Jahjahhhh/projet5/table-2/kicad_libraries/My_Libraries/Header_cassable_4Short_pins__simpleAG2 v1.step

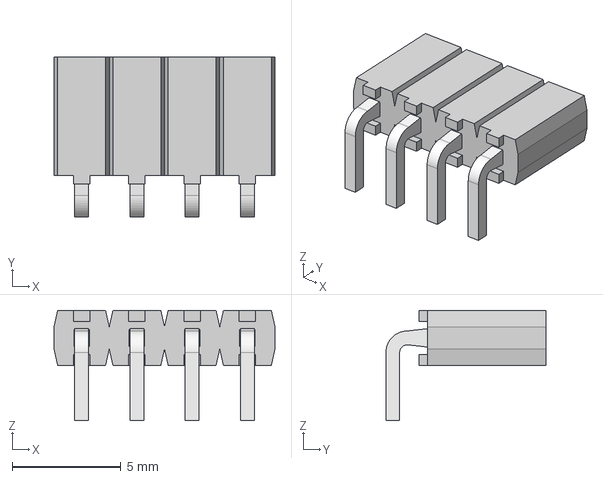
[picture p16: CAD file, 2024-10-07]
table-2/kicad_libraries/My_Libraries/Header_cassable_4Short_pins__simpleAG2 v1.step
10.2 x 7.37 x 5.08 mm
_SSA-132-W-T-RA_t
_SSA-132-W-T-RA_p
