Jahjahhhh/projet5/table-2/kicad_libraries/My_Libraries/SOT_223_5.STEP

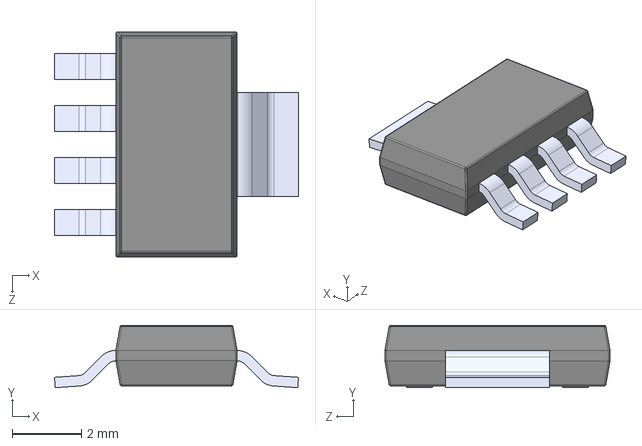
[picture p17: CAD file, 2024-10-07]
table-2/kicad_libraries/My_Libraries/SOT_223_5.STEP
7.04 x 1.80 x 6.50 mm
