Jahjahhhh/projet5/table-2/kicad_libraries/My_Libraries/cree xlamp_xp_e.stl

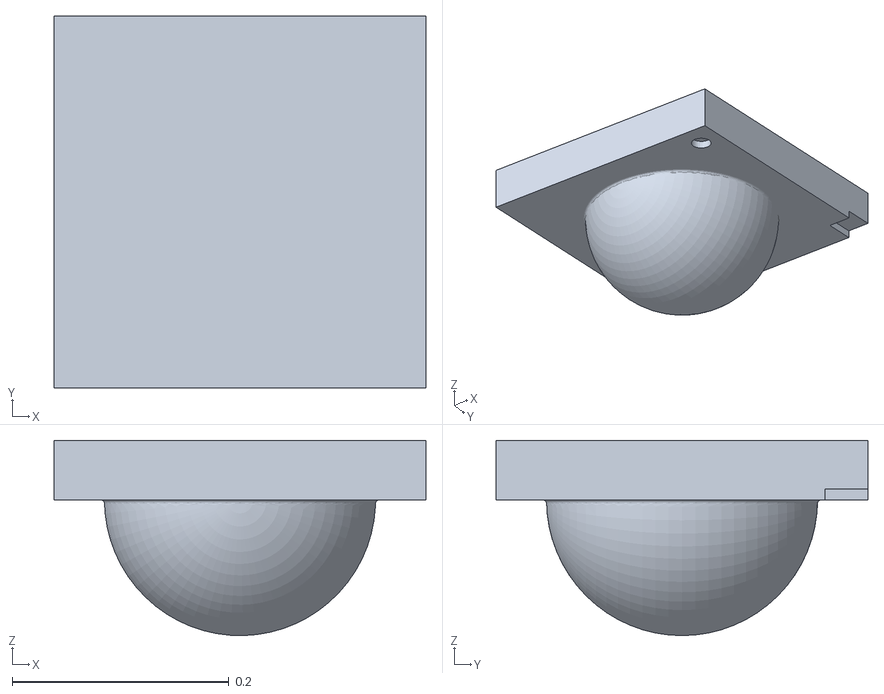
[picture p18: CAD file, 2024-10-07]
table-2/kicad_libraries/My_Libraries/cree xlamp_xp_e.stl
0.343 x 0.343 x 0.18
