Jahjahhhh/projet5/table-2/kicad_libraries/My_Libraries/b3f-6020AG.step

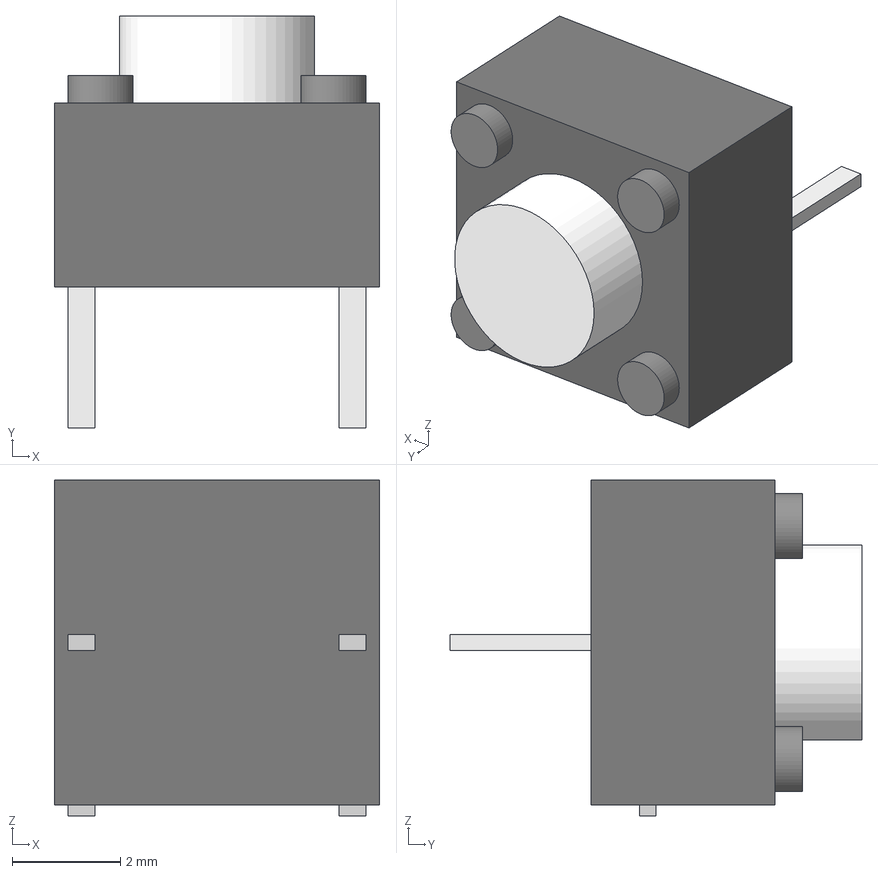
[picture p19: CAD file, 2024-10-07]
table-2/kicad_libraries/My_Libraries/b3f-6020AG.step
6.00 x 7.60 x 6.20 mm
