Jahjahhhh/projet5/table-2/kicad_libraries/My_Libraries/RELAY_ALQ3_PANVA.step

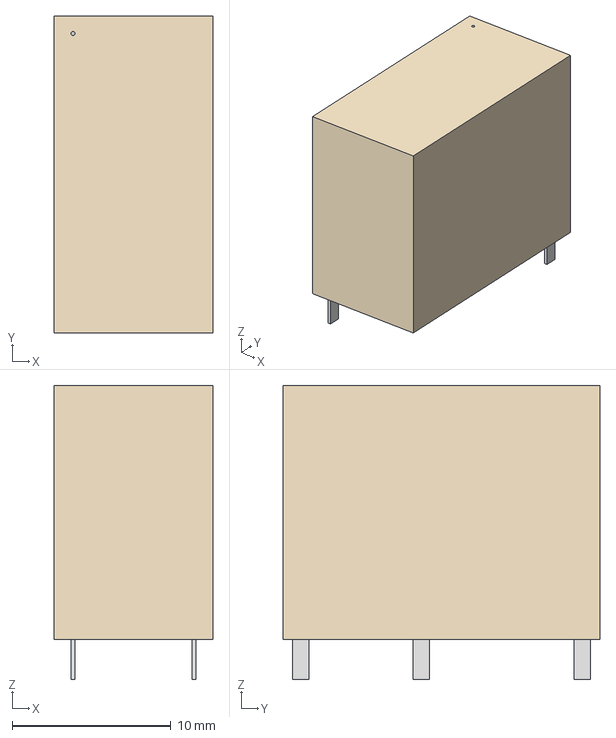
[picture p20: CAD file, 2024-10-07]
table-2/kicad_libraries/My_Libraries/RELAY_ALQ3_PANVA.step
10.0 x 20.0 x 18.5 mm
