Jahjahhhh/projet5/table-2/kicad_libraries/My_Libraries/Nichicon_5x11_LeadAG.step

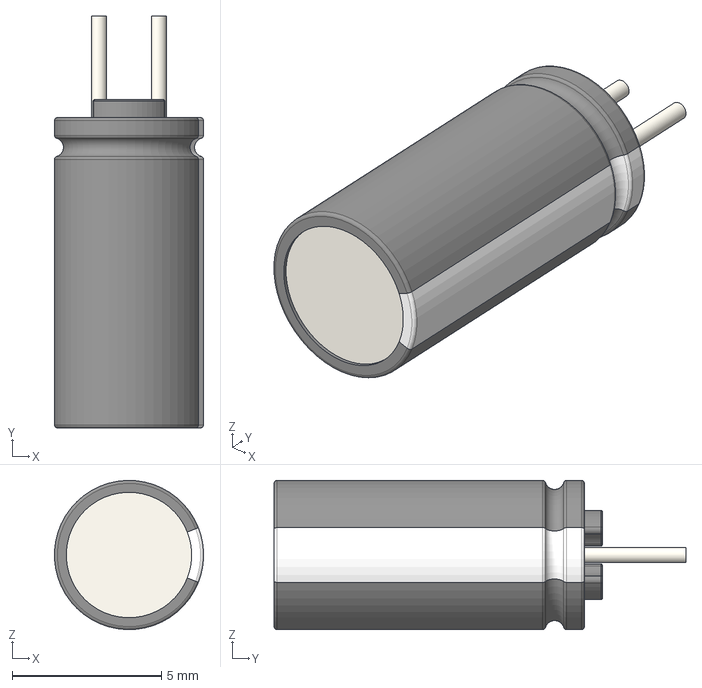
[picture p21: CAD file, 2024-10-07]
table-2/kicad_libraries/My_Libraries/Nichicon_5x11_LeadAG.step
4.99 x 13.8 x 5.00 mm
