Jahjahhhh/projet5/table-2/kicad_libraries/My_Libraries/XTAL_HC49US_ABLS_ABR.step

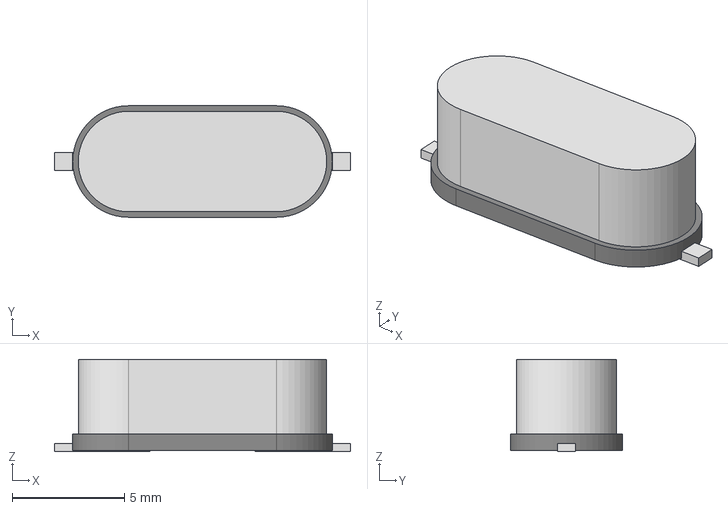
[picture p22: CAD file, 2024-10-07]
table-2/kicad_libraries/My_Libraries/XTAL_HC49US_ABLS_ABR.step
13.2 x 4.98 x 4.12 mm
