Jahjahhhh/projet5/table-2/kicad_libraries/My_Libraries/MEM2075-00-140-01-A.stp

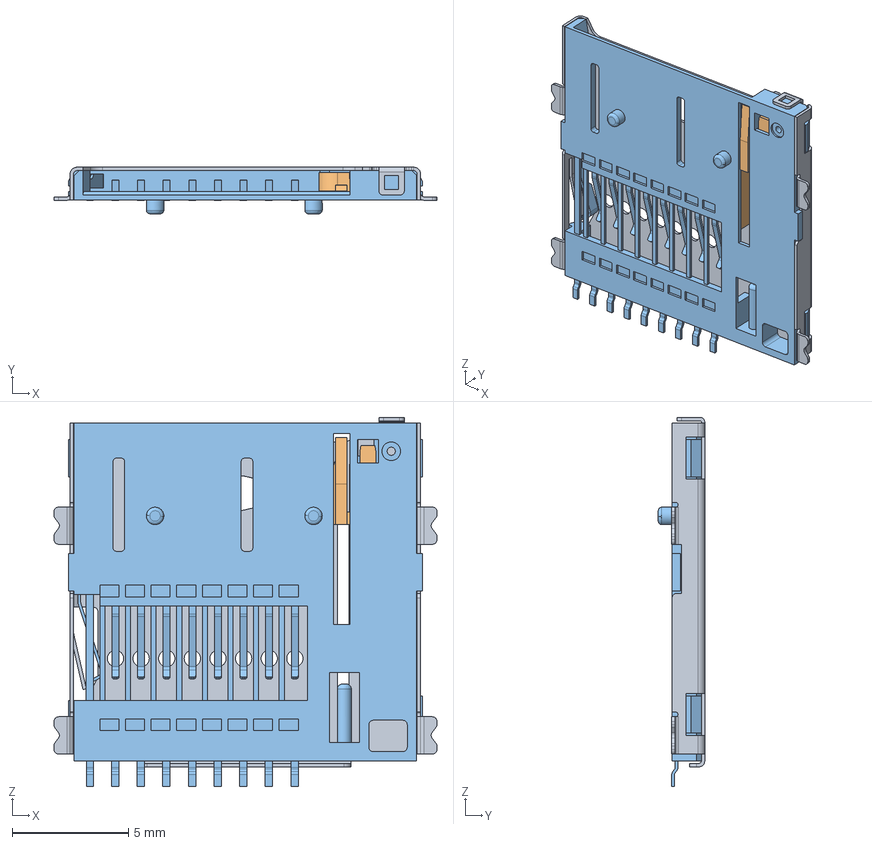
[picture p23: CAD file, 2024-10-07]
table-2/kicad_libraries/My_Libraries/MEM2075-00-140-01-A.stp
16.4 x 2.00 x 15.9 mm
Ëõ·Å±ÈÀý1
Í¹Ì¨-ÀÉì1
Á¬½ÓÖØ×é1
