Jahjahhhh/projet5/table-2/kicad_libraries/My_Libraries/c-1776252-2-a-3d.stp

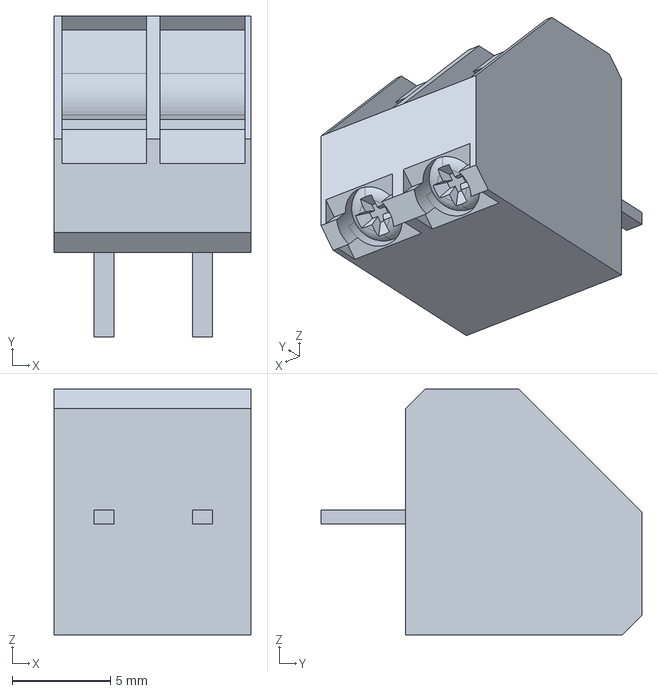
[picture p24: CAD file, 2024-10-07]
table-2/kicad_libraries/My_Libraries/c-1776252-2-a-3d.stp
10.0 x 16.3 x 12.5 mm
