Jahjahhhh/projet5/table-2/kicad_libraries/My_Libraries/3214J.stp

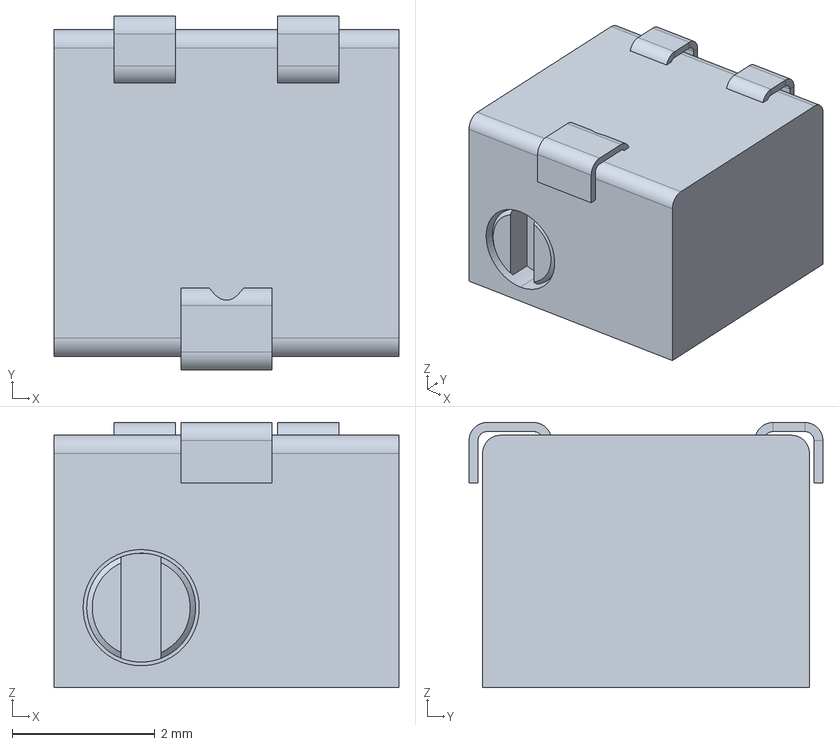
[picture p25: CAD file, 2024-10-07]
table-2/kicad_libraries/My_Libraries/3214J.stp
4.83 x 4.95 x 3.71 mm
