Jahjahhhh/projet5/table-2/kicad_libraries/My_Libraries/ESQ-118-14-G-D.stp

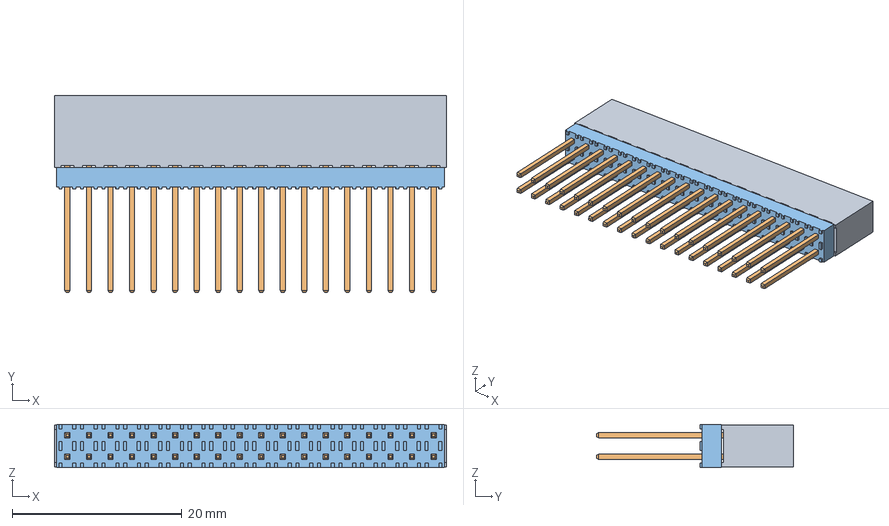
[picture p26: CAD file, 2024-10-07]
table-2/kicad_libraries/My_Libraries/ESQ-118-14-G-D.stp
46.2 x 23.2 x 5.08 mm
_ESQ-118-14-G-D_socket
_ESQ-118-14-G-D_pins
_ESQ-118-14-G-D-LL_bpins
