Jahjahhhh/projet5/table-2/kicad_libraries/My_Libraries/User Library-XBeeProS1-1.STEP

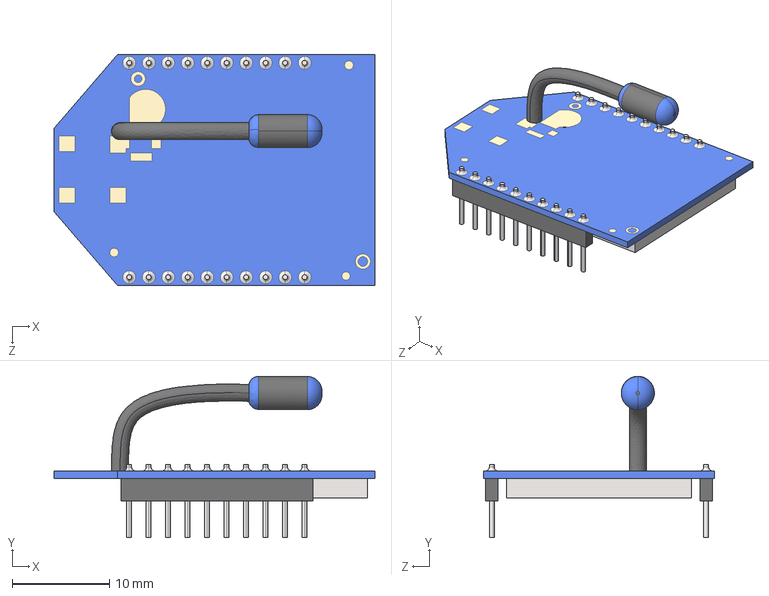
[picture p27: CAD file, 2024-10-07]
table-2/kicad_libraries/My_Libraries/User Library-XBeeProS1-1.STEP
32.9 x 16.6 x 23.7 mm
