Jahjahhhh/projet5/table-2/kicad_libraries/My_Libraries/USB3145-30-0-A.stp

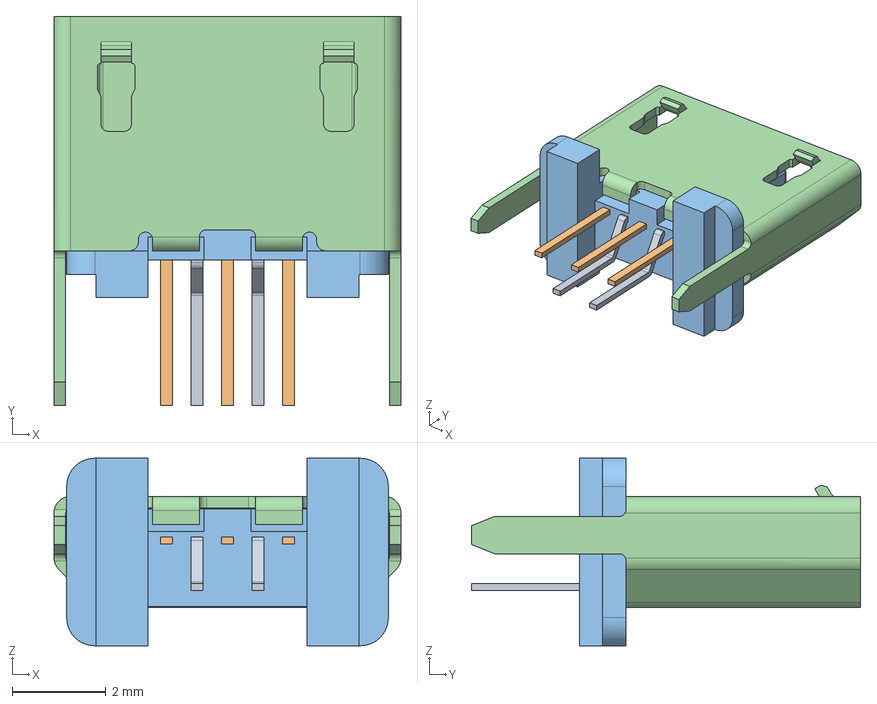
[picture p28: CAD file, 2024-10-07]
table-2/kicad_libraries/My_Libraries/USB3145-30-0-A.stp
7.40 x 8.30 x 4.00 mm
Imported1 x 5
移动面1
倒角1
