Jahjahhhh/projet5/table-2/kicad_libraries/My_Libraries/1-1825027-1_Bouton_Bleu v1.step

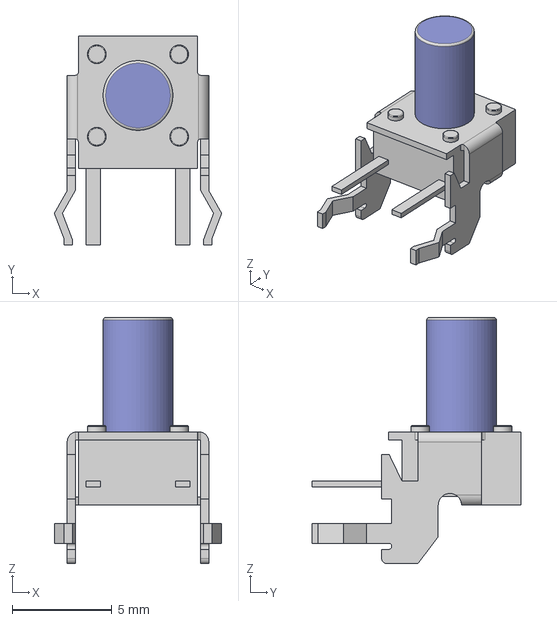
[picture p29: CAD file, 2024-10-07]
table-2/kicad_libraries/My_Libraries/1-1825027-1_Bouton_Bleu v1.step
8.41 x 10.5 x 12.4 mm
