Jahjahhhh/projet5/table-2/kicad_libraries/My_Libraries/B2B-ZR.STEP

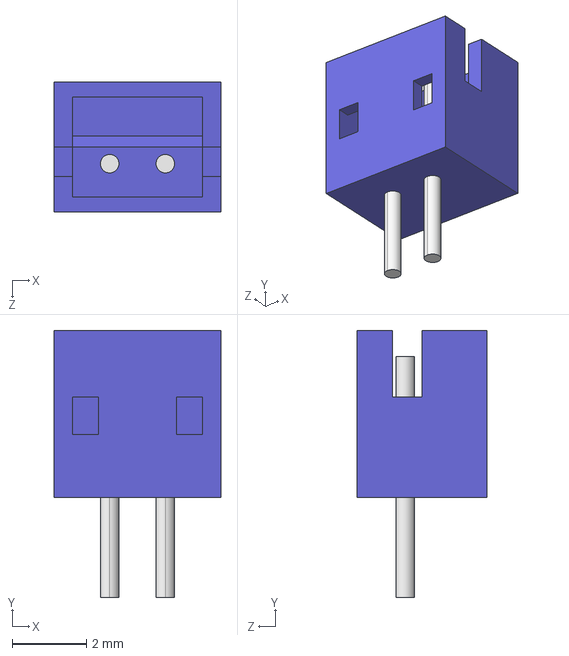
[picture p30: CAD file, 2024-10-07]
table-2/kicad_libraries/My_Libraries/B2B-ZR.STEP
4.50 x 7.20 x 3.50 mm
