Jahjahhhh/projet5/table-2/kicad_libraries/My_Libraries/c-1776252-3-a-3d.stp

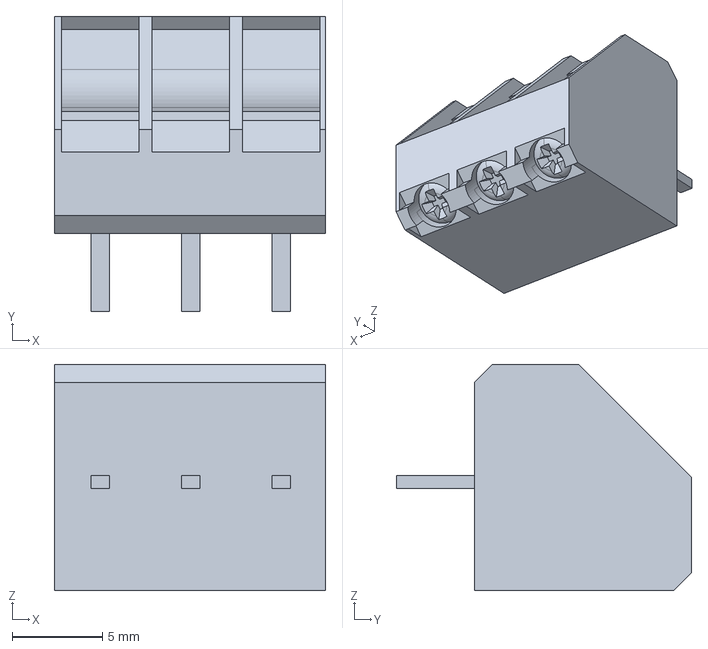
[picture p31: CAD file, 2024-10-07]
table-2/kicad_libraries/My_Libraries/c-1776252-3-a-3d.stp
15.0 x 16.3 x 12.5 mm
