Jahjahhhh/projet5/table-2/kicad_libraries/My_Libraries/panasonic_ALQ1.STEP

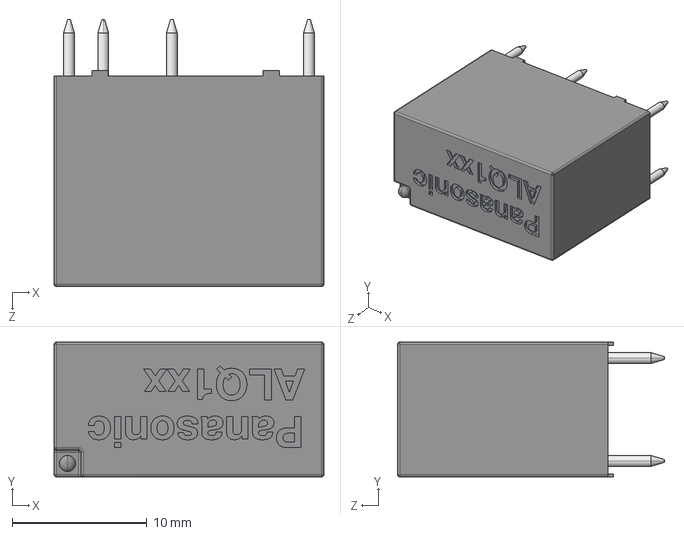
[picture p32: CAD file, 2024-10-07]
table-2/kicad_libraries/My_Libraries/panasonic_ALQ1.STEP
20.0 x 10.0 x 19.8 mm
