Jahjahhhh/projet5/table-2/kicad_libraries/My_Libraries/pxc_1984989_04_PTSA-1-5-4-3-5-F_3D.stp

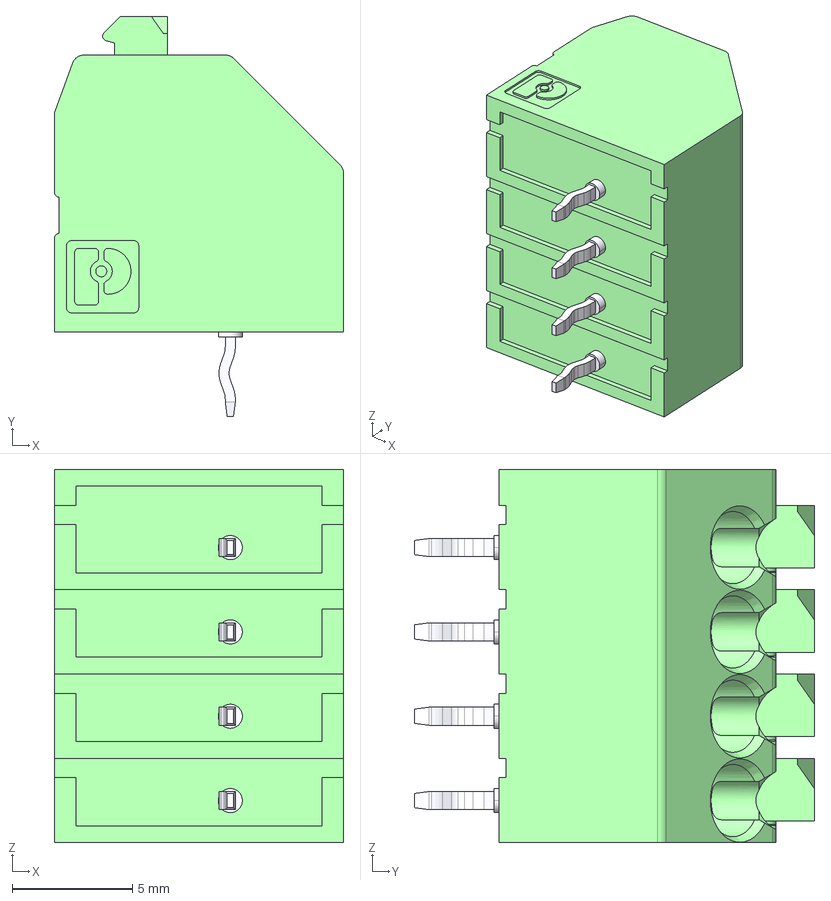
[picture p33: CAD file, 2024-10-07]
table-2/kicad_libraries/My_Libraries/pxc_1984989_04_PTSA-1-5-4-3-5-F_3D.stp
12.0 x 16.6 x 15.5 mm
