Jahjahhhh/projet5/table-2/kicad_libraries/My_Libraries/Barrel_Wurth_5_5X2_1mm.stp

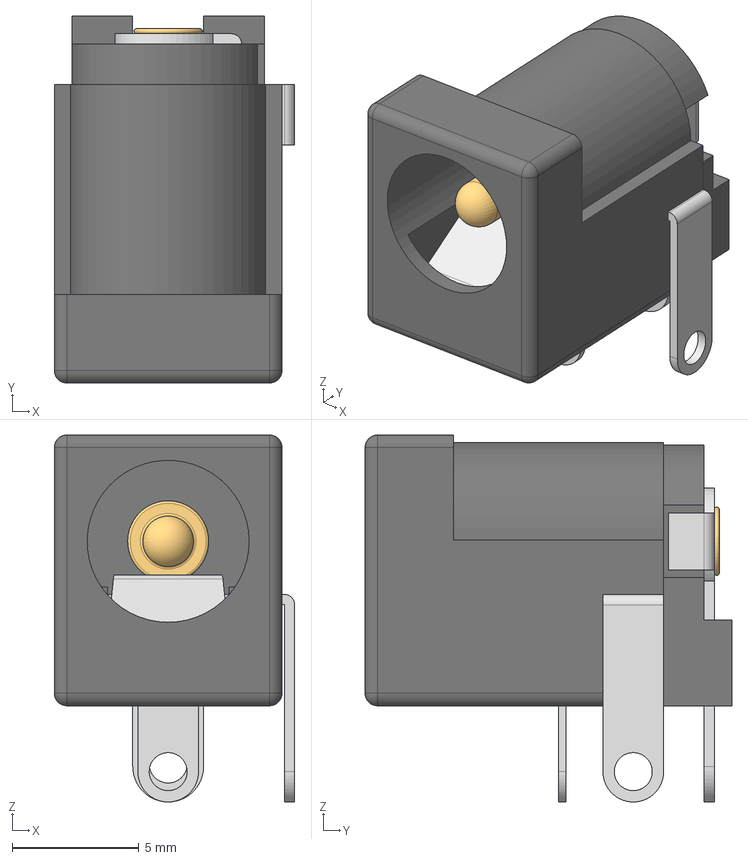
[picture p34: CAD file, 2024-10-07]
table-2/kicad_libraries/My_Libraries/Barrel_Wurth_5_5X2_1mm.stp
9.50 x 14.5 x 14.5 mm
6941xx301002
694106301002_PinContact
6941xx301002_Back
6941xx301002_PinContact2
6941xx301002_PinLame
6941xx301002_PinBis
