Jahjahhhh/projet5/table-2/kicad_libraries/My_Libraries/Stabilizer_close.STEP

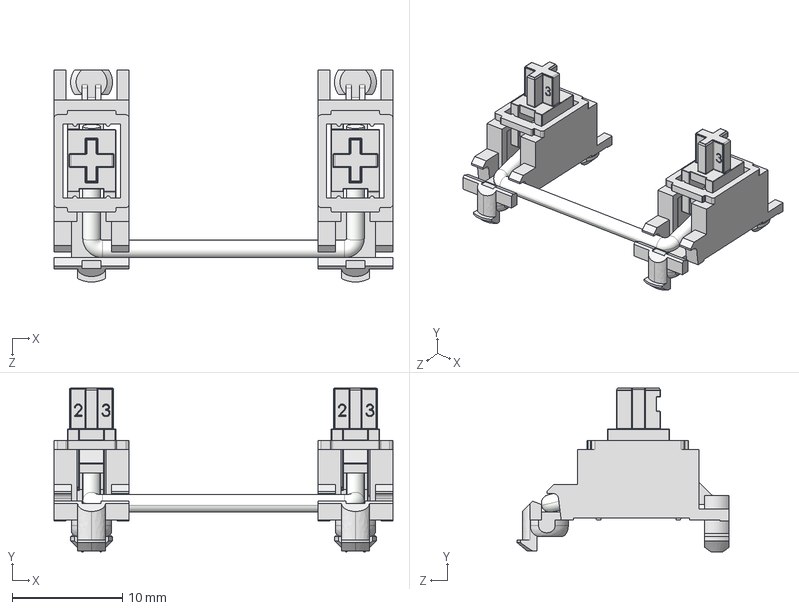
[picture p35: CAD file, 2024-10-07]
table-2/kicad_libraries/My_Libraries/Stabilizer_close.STEP
30.7 x 14.9 x 19.2 mm
mx Stabilizer base 16828 x 2
mx Stabilizer key 16828 x 2
metal stick 16828
