Jahjahhhh/projet5/table-2/kicad_libraries/My_Libraries/PianoSpring_v33.step

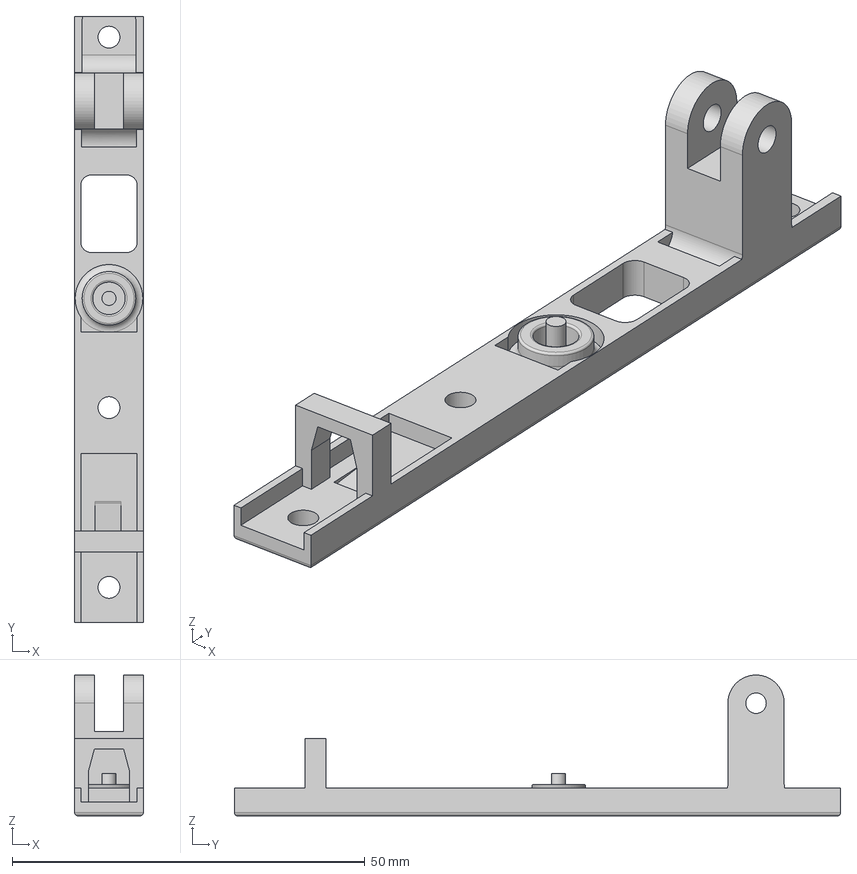
[picture p36: CAD file, 2024-10-07]
table-2/kicad_libraries/My_Libraries/PianoSpring_v33.step
9.75 x 86.0 x 20.0 mm
