Jahjahhhh/projet5/table-2/kicad_libraries/My_Libraries/Adafruit_BNO055__Avec_Header4et6.step

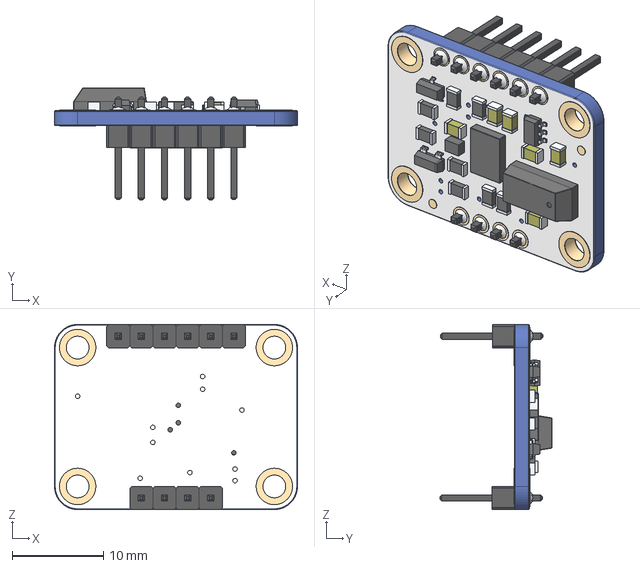
[picture p37: CAD file, 2024-10-07]
table-2/kicad_libraries/My_Libraries/Adafruit_BNO055__Avec_Header4et6.step
26.7 x 12.3 x 20.3 mm
Pin (1) x 4
Pin (1)_1 x 6
