Jahjahhhh/projet5/table-2/kicad_libraries/My_Libraries/1-1318300-2.stp

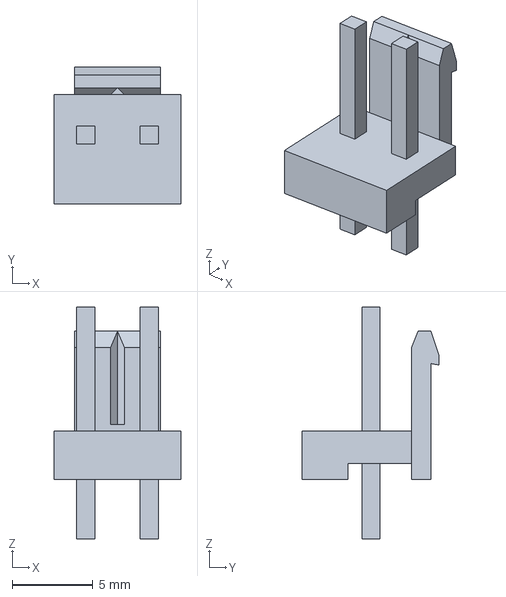
[picture p38: CAD file, 2024-10-07]
table-2/kicad_libraries/My_Libraries/1-1318300-2.stp
7.86 x 8.50 x 14.4 mm
