Jahjahhhh/projet5/table-2/kicad_libraries/My_Libraries/ENCODEUR.STEP

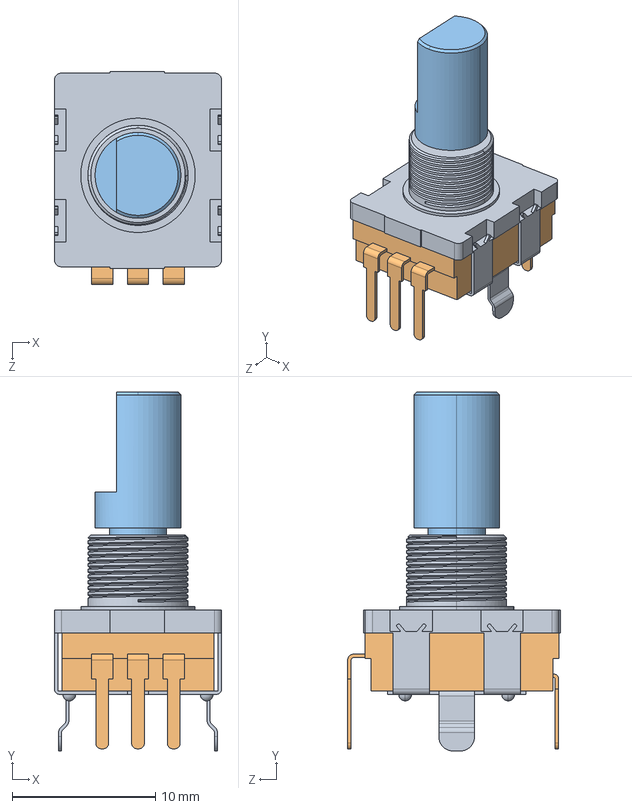
[picture p39: CAD file, 2024-10-07]
table-2/kicad_libraries/My_Libraries/ENCODEUR.STEP
11.7 x 25.1 x 14.9 mm
