Jahjahhhh/projet5/table-2/kicad_libraries/My_Libraries/SM04B_56544.STEP

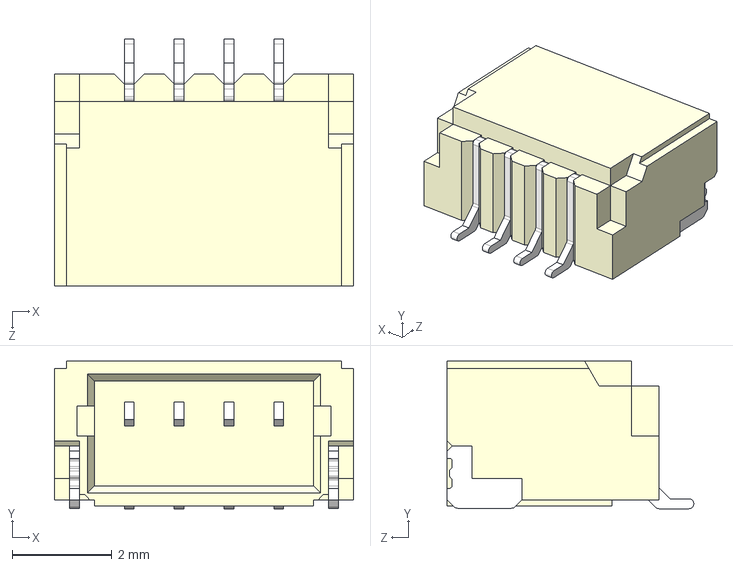
[picture p40: CAD file, 2024-10-07]
table-2/kicad_libraries/My_Libraries/SM04B_56544.STEP
6.00 x 2.96 x 4.95 mm
