Jahjahhhh/projet5/table-2/kicad_libraries/My_Libraries/PS30-10PB1BR10K.stp

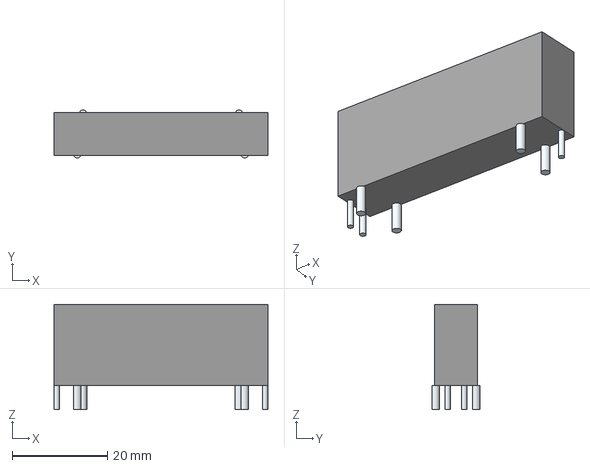
[picture p41: CAD file, 2024-10-07]
table-2/kicad_libraries/My_Libraries/PS30-10PB1BR10K.stp
45.0 x 10.1 x 22.1 mm
Leads x 7
