Jahjahhhh/projet5/table-2/kicad_libraries/My_Libraries/TS6-SMT_H-6.0.step

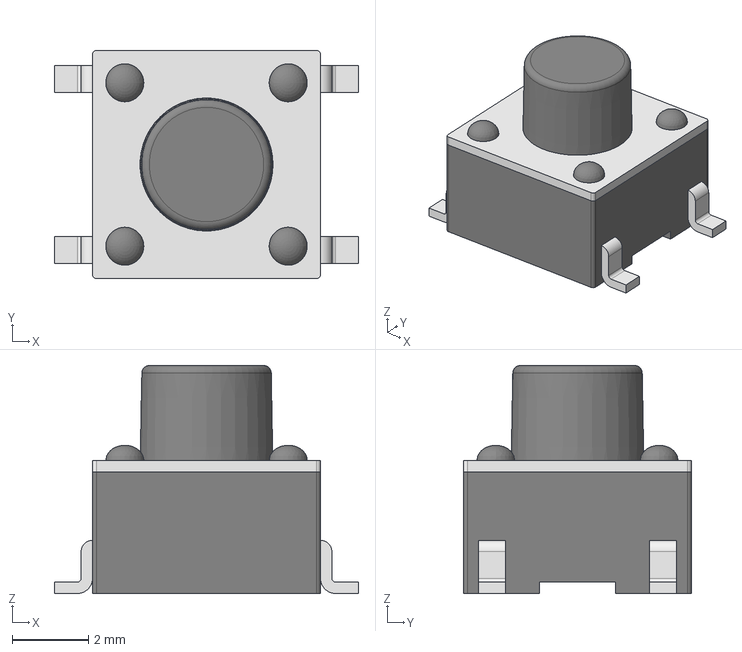
[picture p42: CAD file, 2024-10-07]
table-2/kicad_libraries/My_Libraries/TS6-SMT_H-6.0.step
8.00 x 6.00 x 6.00 mm
