Jahjahhhh/projet5/table-2/kicad_libraries/My_Libraries/Barrel_54-00134.STEP

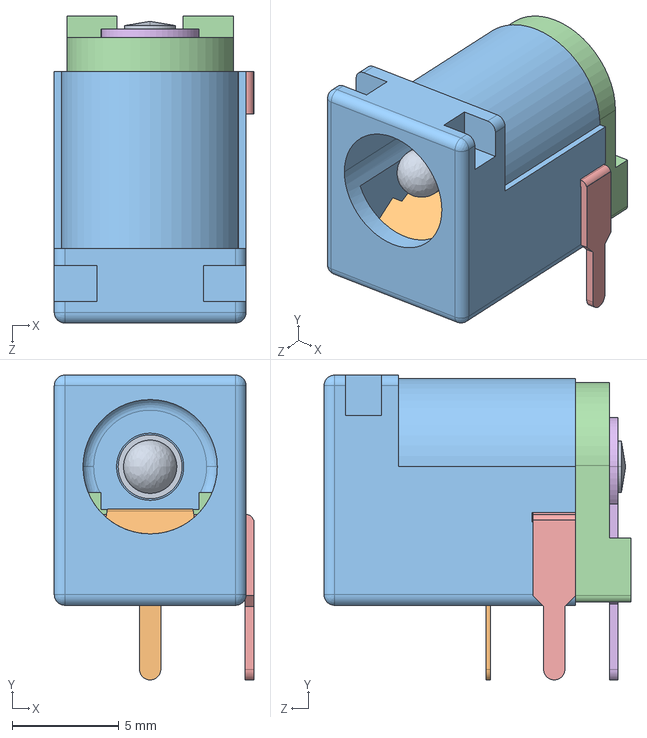
[picture p43: CAD file, 2024-10-07]
table-2/kicad_libraries/My_Libraries/Barrel_54-00134.STEP
9.36 x 14.3 x 14.4 mm
