Jahjahhhh/projet5/table-2/kicad_libraries/My_Libraries/CREE_XPE_AG.step

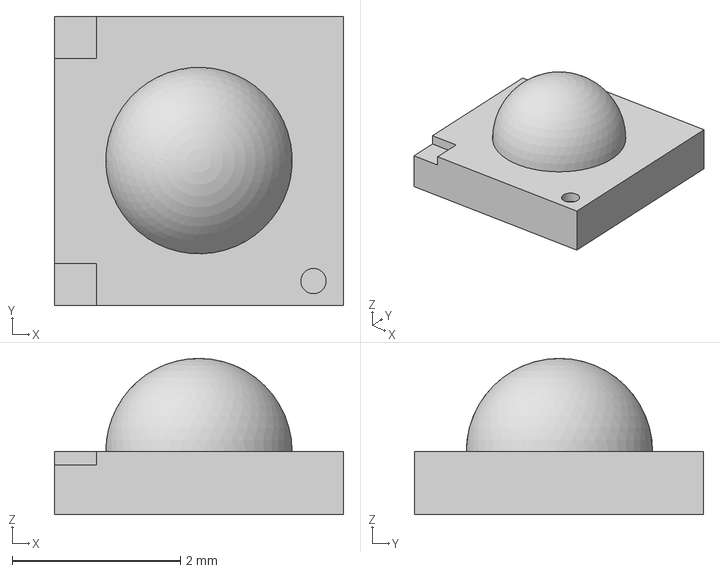
[picture p44: CAD file, 2024-10-07]
table-2/kicad_libraries/My_Libraries/CREE_XPE_AG.step
3.44 x 3.44 x 1.86 mm
