Jahjahhhh/projet5/table-2/kicad_libraries/My_Libraries/MS085xx03FxxxS1A.stp

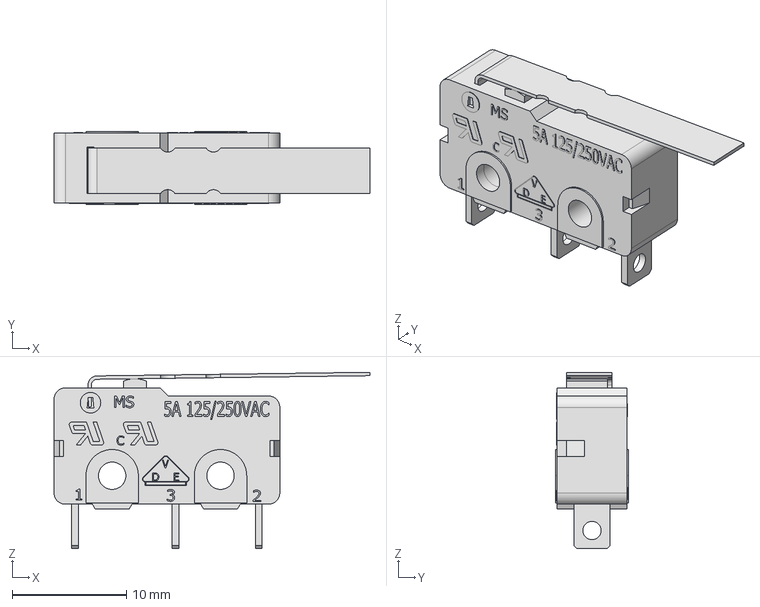
[picture p45: CAD file, 2024-10-07]
table-2/kicad_libraries/My_Libraries/MS085xx03FxxxS1A.stp
27.7 x 6.40 x 15.5 mm
