Jahjahhhh/projet5/table-2/kicad_libraries/My_Libraries/JB15KP-1A.stp

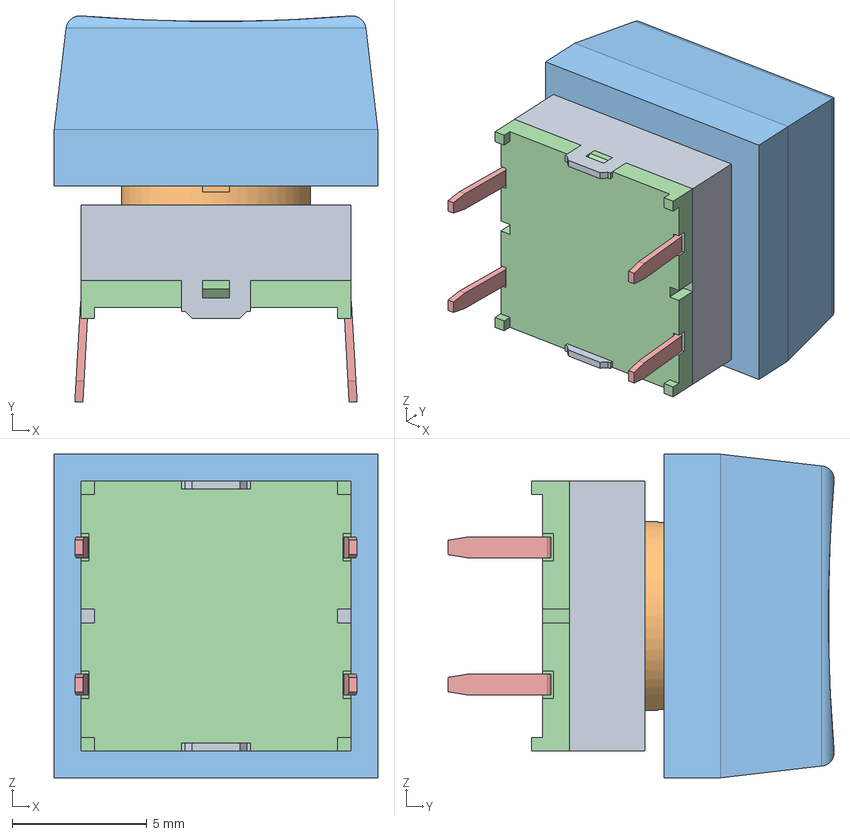
[picture p46: CAD file, 2024-10-07]
table-2/kicad_libraries/My_Libraries/JB15KP-1A.stp
12.0 x 14.3 x 12.0 mm
_JB15KP-1Ashex
_JBKPsht
_JB15KP-1Acap1
_JB15KPterm
_JB15KP-1Atrmn x 4
