Jahjahhhh/projet5/table-2/kicad_libraries/My_Libraries/Wurth_1X2_5mmH.stp

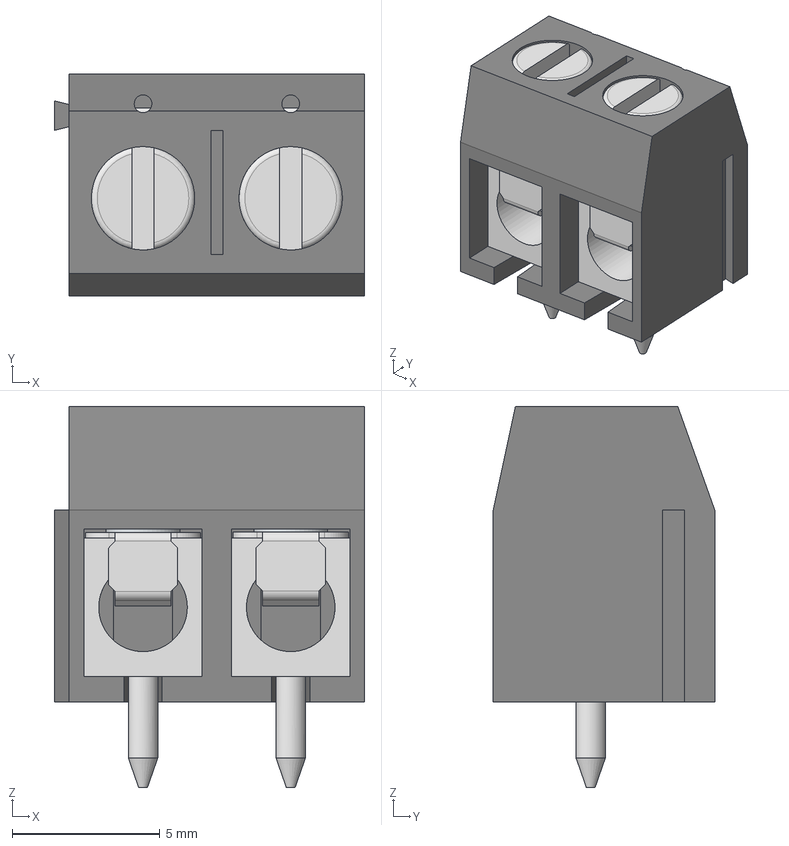
[picture p47: CAD file, 2024-10-07]
table-2/kicad_libraries/My_Libraries/Wurth_1X2_5mmH.stp
10.5 x 7.50 x 12.9 mm
6915027100xx_CAGE x 2
6915027100xx_PIN x 2
6915027100xx_VIS x 2
