Jahjahhhh/projet5/table-2/kicad_libraries/My_Libraries/ECS-120-20-30B-AEN-TR.STEP

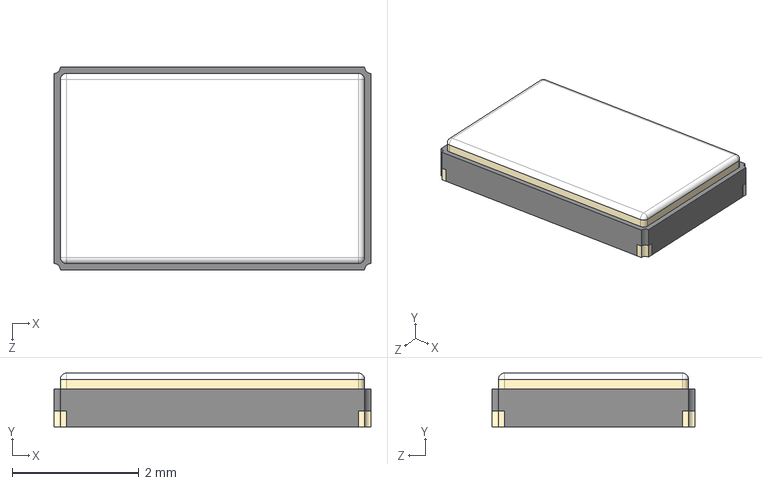
[picture p48: CAD file, 2024-10-07]
table-2/kicad_libraries/My_Libraries/ECS-120-20-30B-AEN-TR.STEP
5.00 x 0.85 x 3.20 mm
