Jahjahhhh/projet5/table-2/kicad_libraries/My_Libraries/Faston_1742188.stp

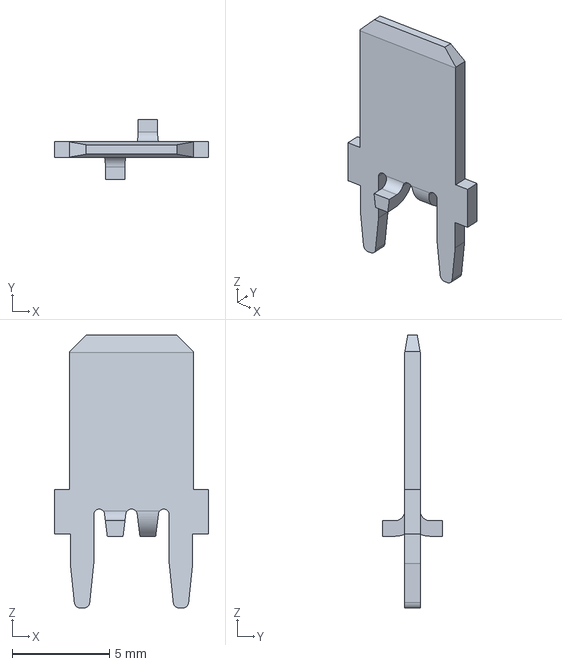
[picture p49: CAD file, 2024-10-07]
table-2/kicad_libraries/My_Libraries/Faston_1742188.stp
7.92 x 3.09 x 14.0 mm
