Jahjahhhh/projet5/table-2/kicad_libraries/My_Libraries/Header6F_100mils.step

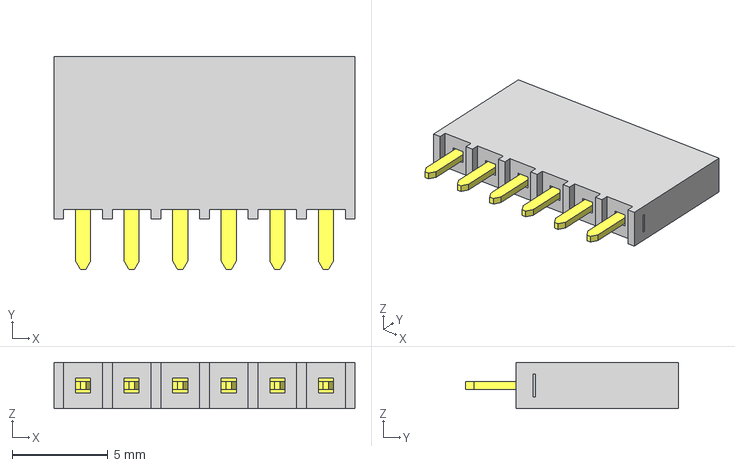
[picture p50: CAD file, 2024-10-07]
table-2/kicad_libraries/My_Libraries/Header6F_100mils.step
15.7 x 11.2 x 2.41 mm
_T1SSW-110-01-F-S
_P2SSW-110-01-F-S
