Jahjahhhh/projet5/table-2/kicad_libraries/My_Libraries/S2B-PH-SM4-TB.STEP

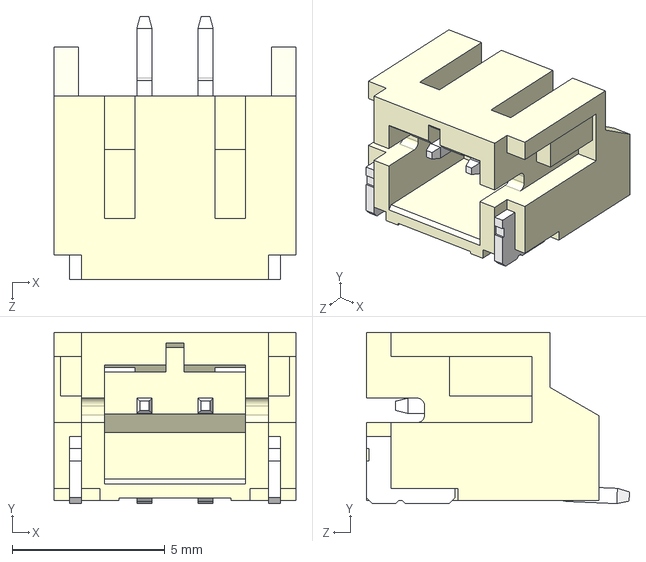
[picture p51: CAD file, 2024-10-07]
table-2/kicad_libraries/My_Libraries/S2B-PH-SM4-TB.STEP
7.90 x 5.60 x 8.60 mm
