Jahjahhhh/projet5/table-2/kicad_libraries/My_Libraries/CUI_BARREL3_4X1.step

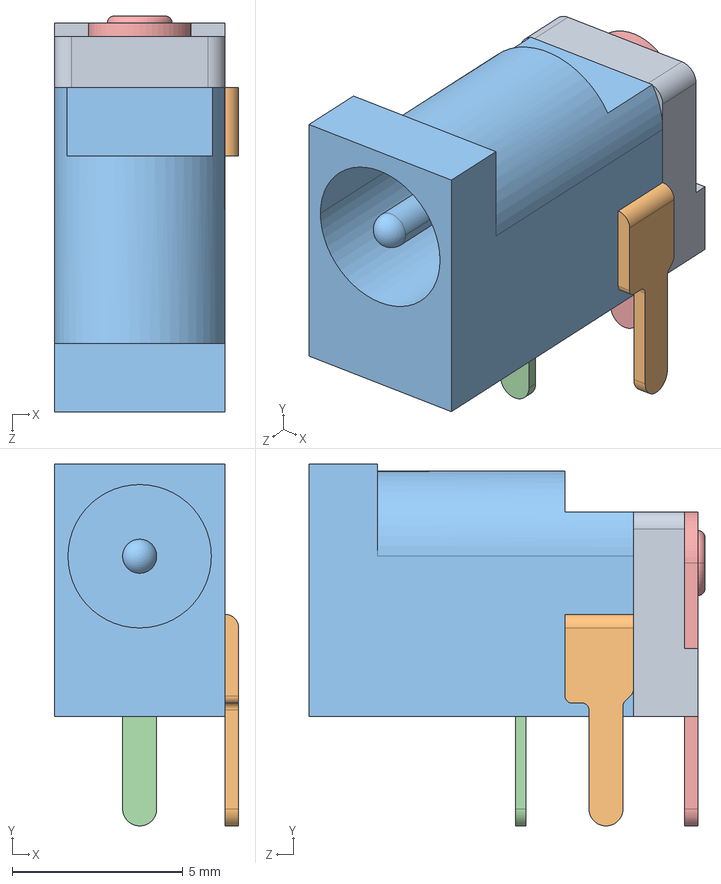
[picture p52: CAD file, 2024-10-07]
table-2/kicad_libraries/My_Libraries/CUI_BARREL3_4X1.step
5.40 x 10.6 x 11.6 mm
