Jahjahhhh/projet5/table-2/kicad_libraries/My_Libraries/ECS_327.STEP

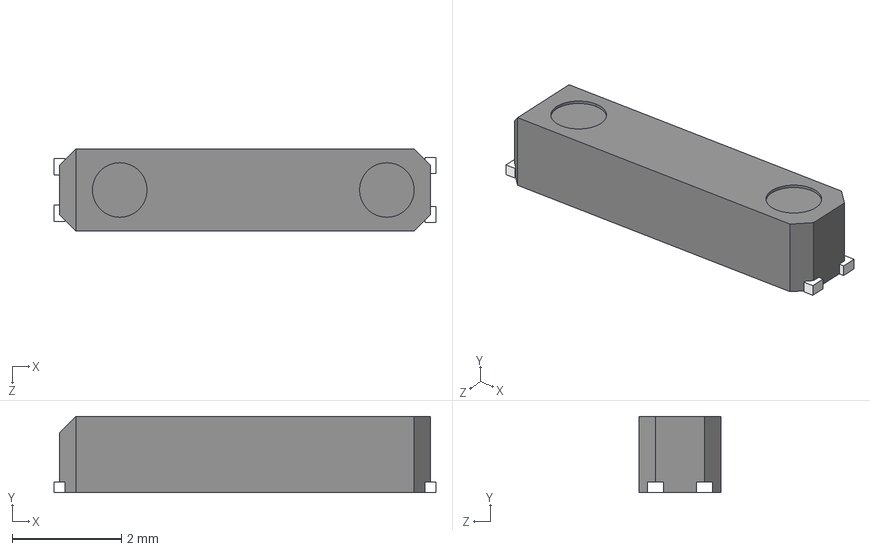
[picture p53: CAD file, 2024-10-07]
table-2/kicad_libraries/My_Libraries/ECS_327.STEP
7.00 x 1.40 x 1.50 mm
