Jahjahhhh/projet5/table-2/kicad_libraries/My_Libraries/Header_Cassable_7Short_PinsAG1.step

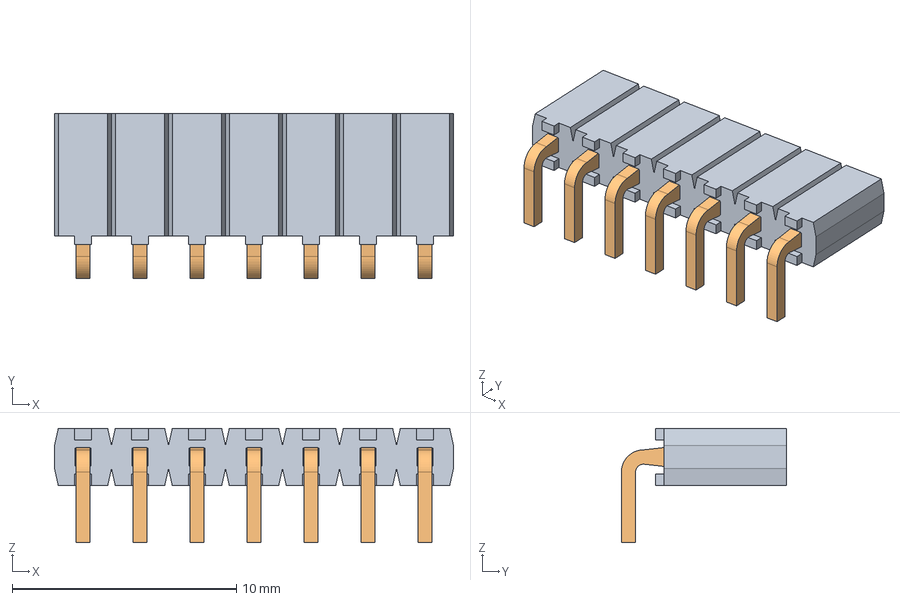
[picture p54: CAD file, 2024-10-07]
table-2/kicad_libraries/My_Libraries/Header_Cassable_7Short_PinsAG1.step
17.8 x 7.37 x 5.08 mm
_SSA-132-W-T-RA_t
_SSA-132-W-T-RA_p
