Jahjahhhh/projet5/table-2/kicad_libraries/My_Libraries/PinSocket_1x10_P2.00mm_pour_XBEE_AG v1.step

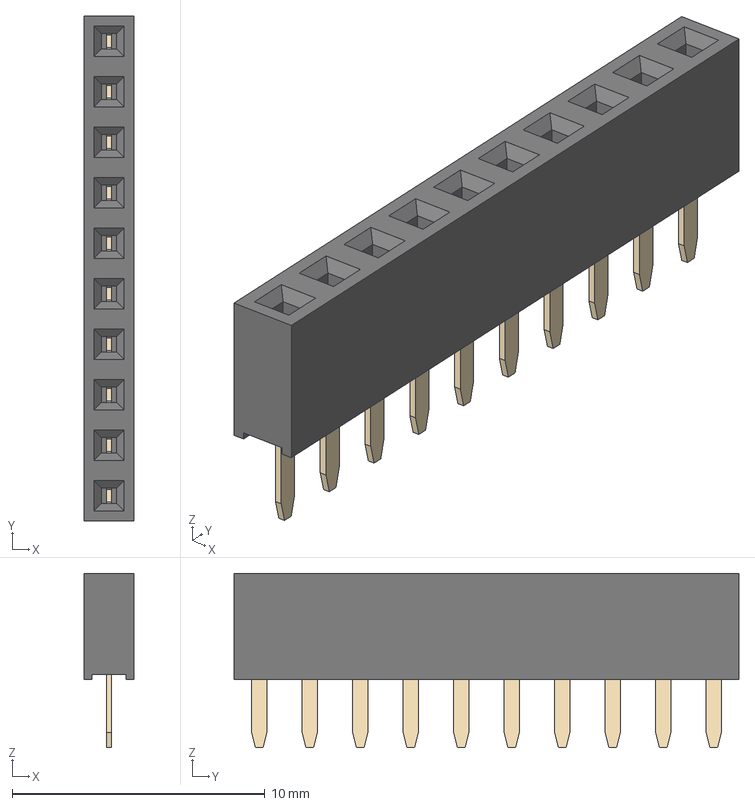
[picture p55: CAD file, 2024-10-07]
table-2/kicad_libraries/My_Libraries/PinSocket_1x10_P2.00mm_pour_XBEE_AG v1.step
2.00 x 20.0 x 6.90 mm
