Jahjahhhh/projet5/table-2/kicad_libraries/My_Libraries/SKRRABE010A.step

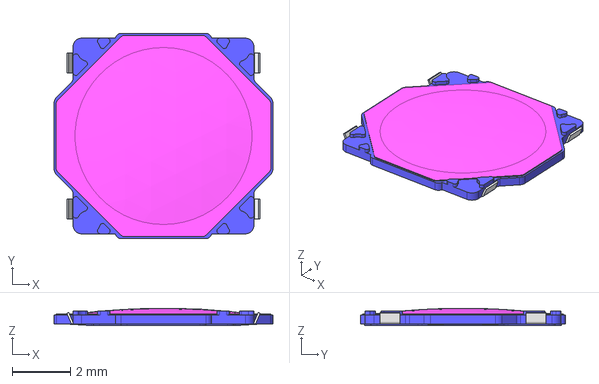
[picture p56: CAD file, 2024-10-07]
table-2/kicad_libraries/My_Libraries/SKRRABE010A.step
7.50 x 7.02 x 0.596 mm
