Jahjahhhh/projet5/table-2/kicad_libraries/My_Libraries/Banniere_IR_V0 v6.step

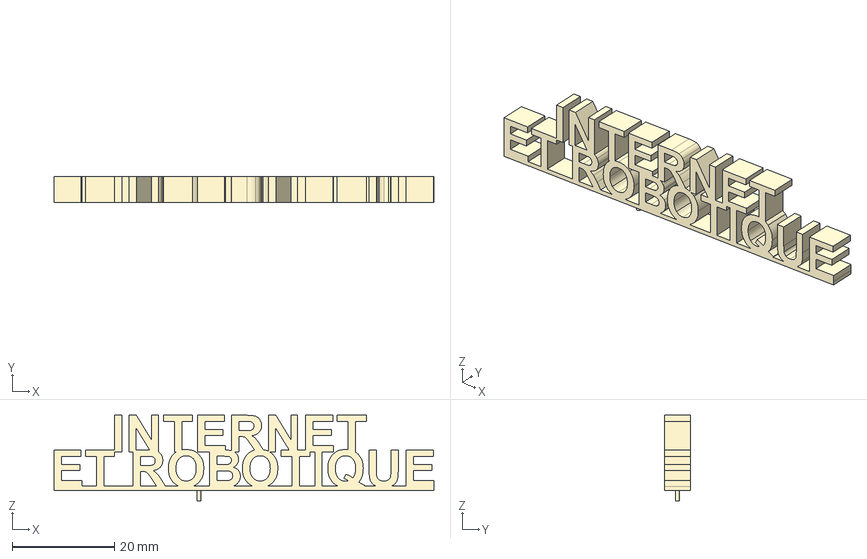
[picture p57: CAD file, 2024-10-07]
table-2/kicad_libraries/My_Libraries/Banniere_IR_V0 v6.step
74.2 x 5.00 x 16.7 mm
