Jahjahhhh/projet5/table-2/kicad_libraries/My_Libraries/3006_MAX98357.step

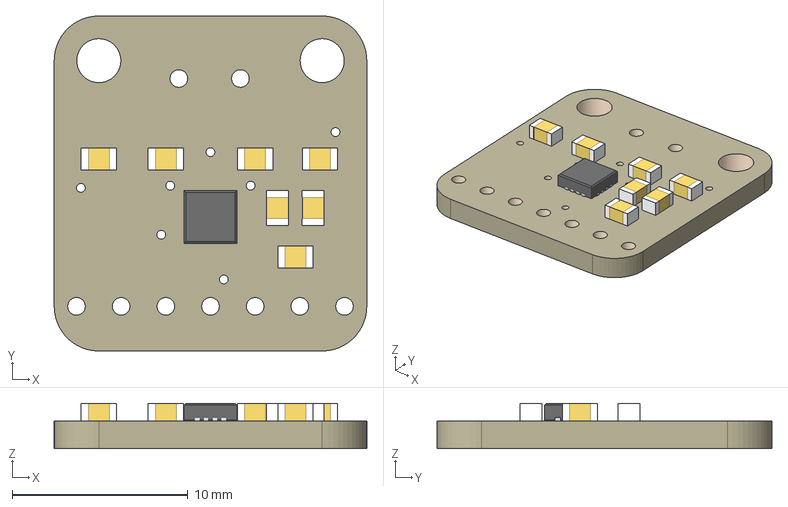
[picture p59: CAD file, 2024-10-07]
table-2/kicad_libraries/My_Libraries/3006_MAX98357.step
17.8 x 19.1 x 2.57 mm
Board
MAX98357A
220pF x 7
