Jahjahhhh/projet5/table-2/kicad_libraries/My_Libraries/Header_cassable_5Long_pins__simpleAG2 v1.step

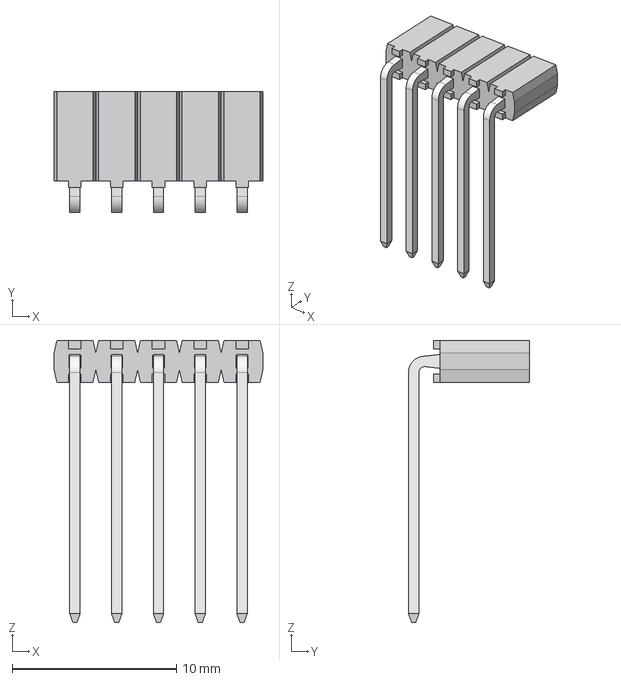
[picture p60: CAD file, 2024-10-07]
table-2/kicad_libraries/My_Libraries/Header_cassable_5Long_pins__simpleAG2 v1.step
12.7 x 7.37 x 17.1 mm
_SSA-132-W-T-RA_t
_SSA-132-W-T-RA_p
