Jahjahhhh/projet5/table-2/kicad_libraries/My_Libraries/ABS25_32_768_AG.step

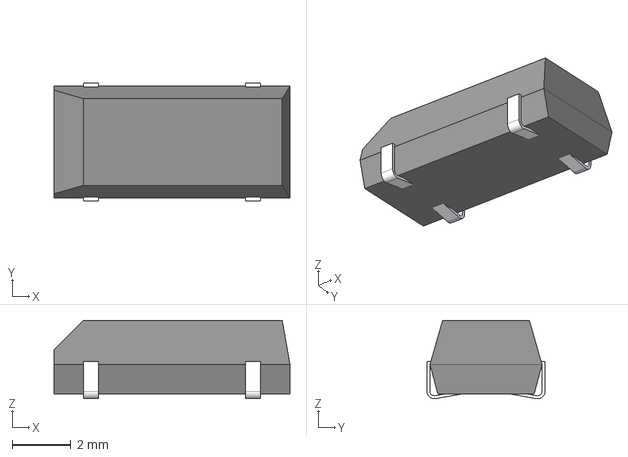
[picture p61: CAD file, 2024-10-07]
table-2/kicad_libraries/My_Libraries/ABS25_32_768_AG.step
8.00 x 4.00 x 2.66 mm
