Jahjahhhh/projet5/table-2/kicad_libraries/My_Libraries/ESQ-108-14-T-S.stp

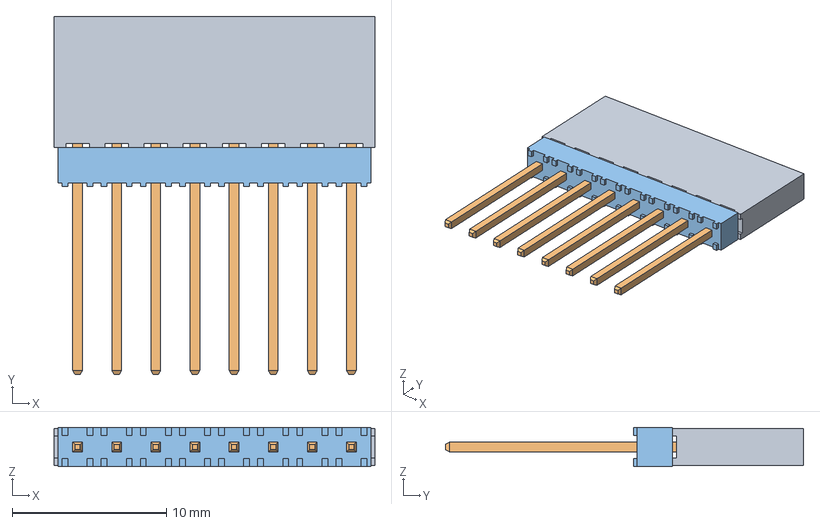
[picture p62: CAD file, 2024-10-07]
table-2/kicad_libraries/My_Libraries/ESQ-108-14-T-S.stp
20.8 x 23.2 x 2.54 mm
_ESQ-108-14-T-S_socket
_ESQ-108-14-T-S_pins
_ESQ-108-14-G-S-LL_bpins
