Jahjahhhh/projet5/table-2/kicad_libraries/My_Libraries/SOT-89-5.step

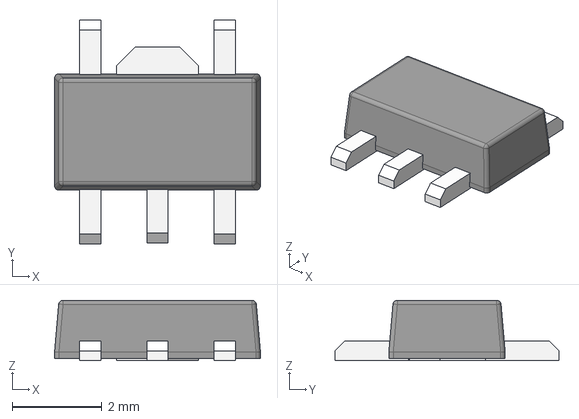
[picture p63: CAD file, 2024-10-07]
table-2/kicad_libraries/My_Libraries/SOT-89-5.step
4.60 x 5.00 x 1.35 mm
