Jahjahhhh/projet5/table-2/kicad_libraries/My_Libraries/USB4105--3DModel-STEP-56544.STEP

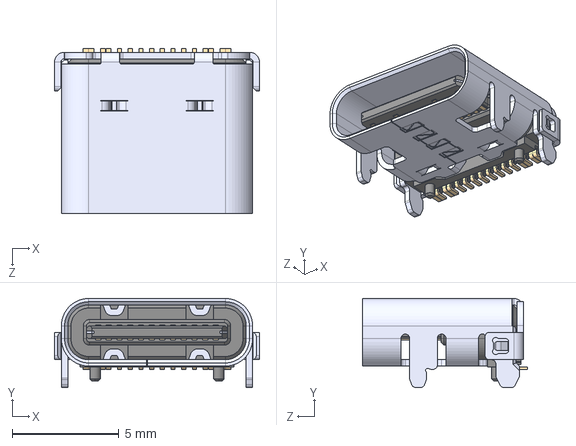
[picture p64: CAD file, 2024-10-07]
table-2/kicad_libraries/My_Libraries/USB4105--3DModel-STEP-56544.STEP
9.58 x 4.16 x 7.71 mm
