Jahjahhhh/projet5/table-2/kicad_libraries/My_Libraries/Trimmer_3306F001.stp

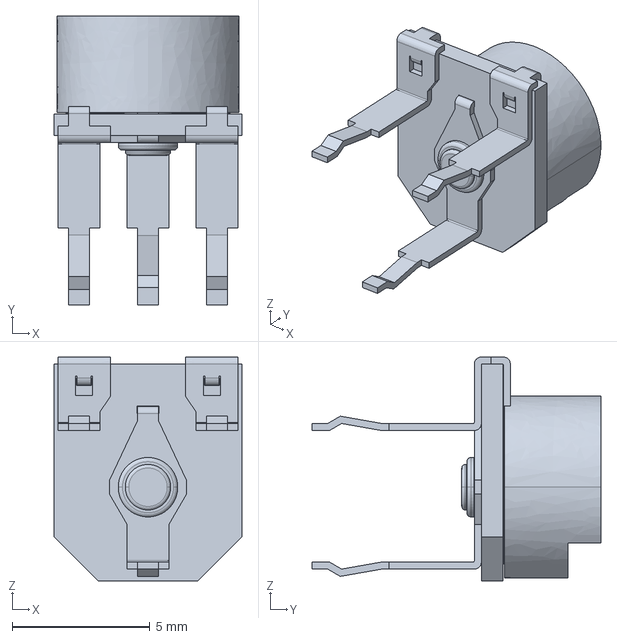
[picture p65: CAD file, 2024-10-07]
table-2/kicad_libraries/My_Libraries/Trimmer_3306F001.stp
6.81 x 10.5 x 8.13 mm
