Jahjahhhh/projet5/table-2/kicad_libraries/My_Libraries/Test_point_Mill_Max_3132AG1.step

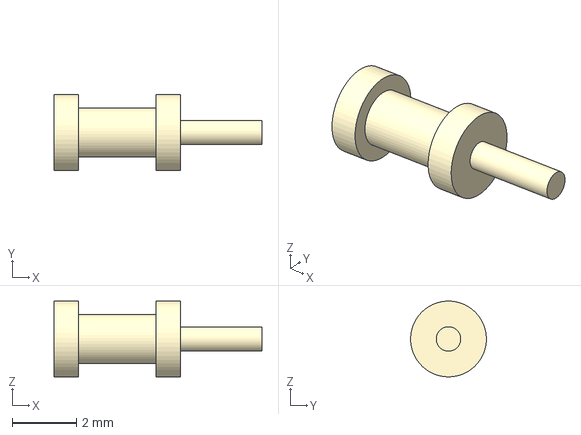
[picture p66: CAD file, 2024-10-07]
table-2/kicad_libraries/My_Libraries/Test_point_Mill_Max_3132AG1.step
6.48 x 2.36 x 2.36 mm
