Jahjahhhh/projet5/table-2/kicad_libraries/My_Libraries/Term_Ressort_2pos.stp

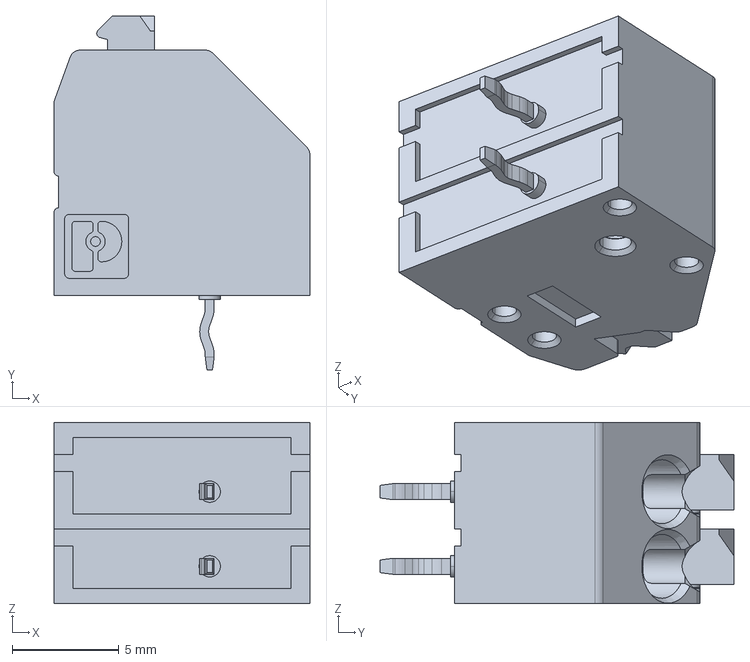
[picture p67: CAD file, 2024-10-07]
table-2/kicad_libraries/My_Libraries/Term_Ressort_2pos.stp
12.0 x 16.6 x 8.50 mm
