Jahjahhhh/projet5/table-2/kicad_libraries/My_Libraries/NanoV3_PAS_ISPC_SUR_EMBASE v1.step

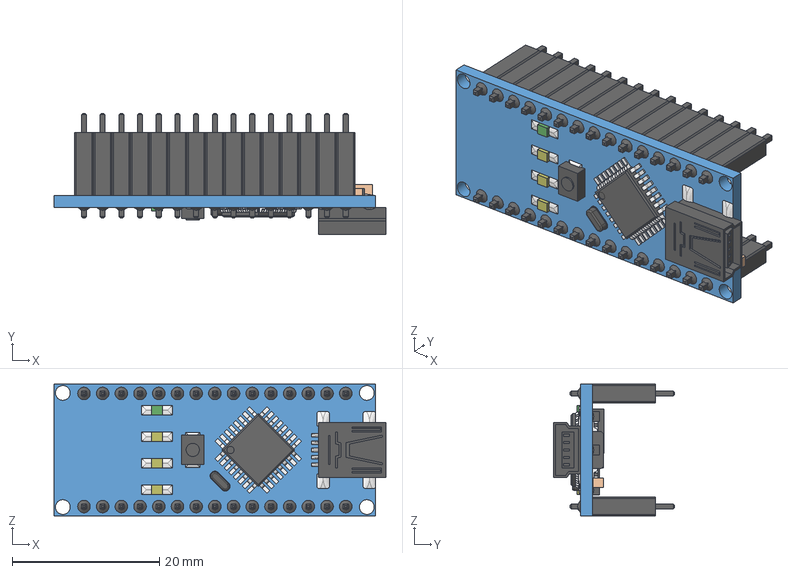
[picture p68: CAD file, 2024-10-07]
table-2/kicad_libraries/My_Libraries/NanoV3_PAS_ISPC_SUR_EMBASE v1.step
45.1 x 16.5 x 17.9 mm
switch
Led x 3
Led (1)
chip1
USB
Crystal
Pin (1) x 15
Pin x 15
Res x 5
cap x 2
Chip
respack x 2
diode
vreg
