Jahjahhhh/projet5/table-2/kicad_libraries/My_Libraries/Barrel_3_5_1_35.STEP

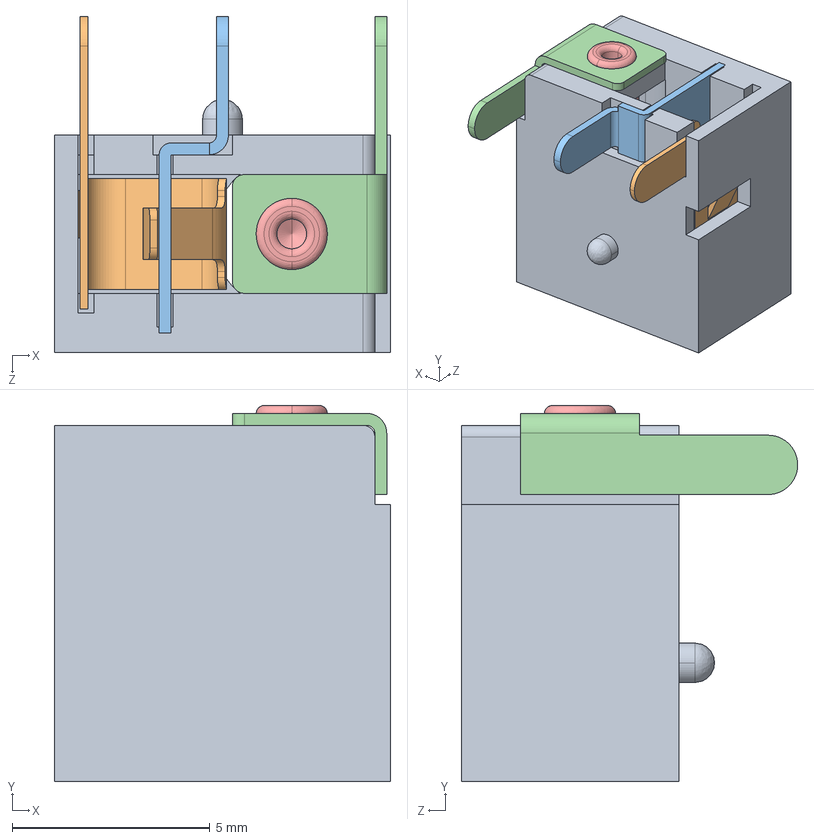
[picture p69: CAD file, 2024-10-07]
table-2/kicad_libraries/My_Libraries/Barrel_3_5_1_35.STEP
8.50 x 9.50 x 8.50 mm
54-00126 insulator
54-00126 terminal
54-00126 terminal 2
54-00126 terminal 3
54-00126 center pin
