Jahjahhhh/projet5/table-2/kicad_libraries/My_Libraries/1301_9503_3.STEP

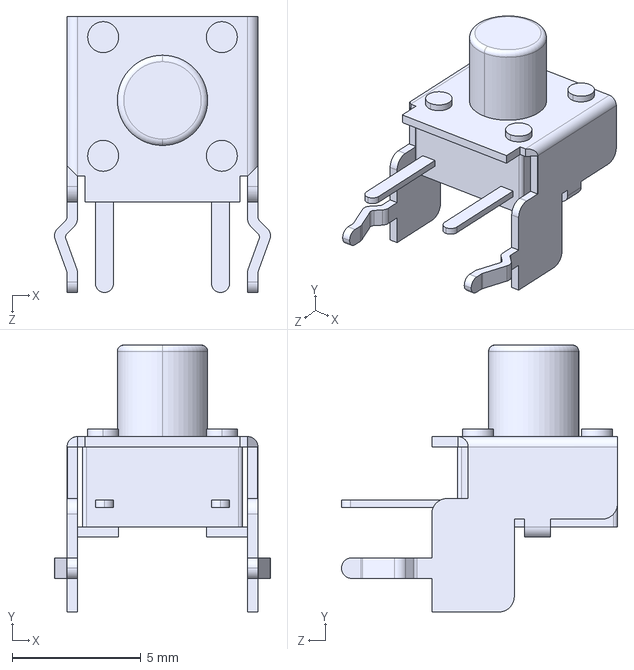
[picture p70: CAD file, 2024-10-07]
table-2/kicad_libraries/My_Libraries/1301_9503_3.STEP
8.37 x 10.3 x 10.7 mm
