Jahjahhhh/projet5/table-2/kicad_libraries/My_Libraries/Joystick__09032.step

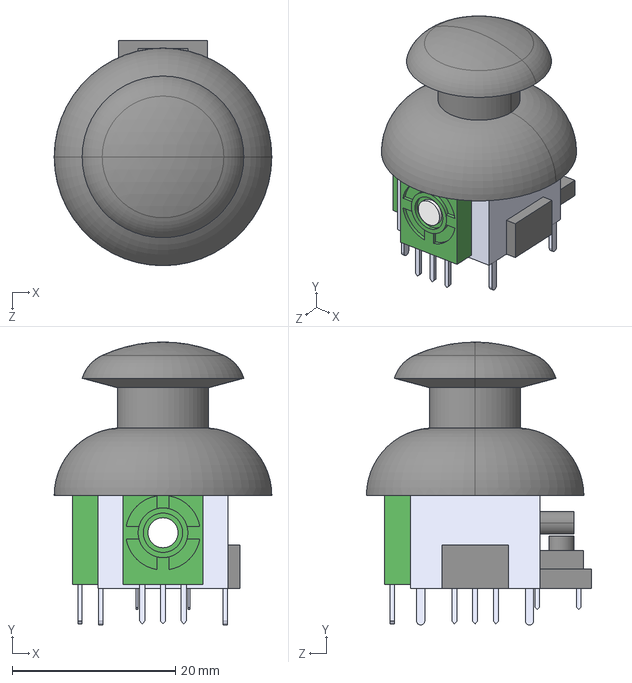
[picture p71: CAD file, 2024-10-07]
table-2/kicad_libraries/My_Libraries/Joystick__09032.step
26.7 x 34.7 x 27.6 mm
