Jahjahhhh/projet5/table-2/kicad_libraries/My_Libraries/SPSTL101011ML04Q.STEP

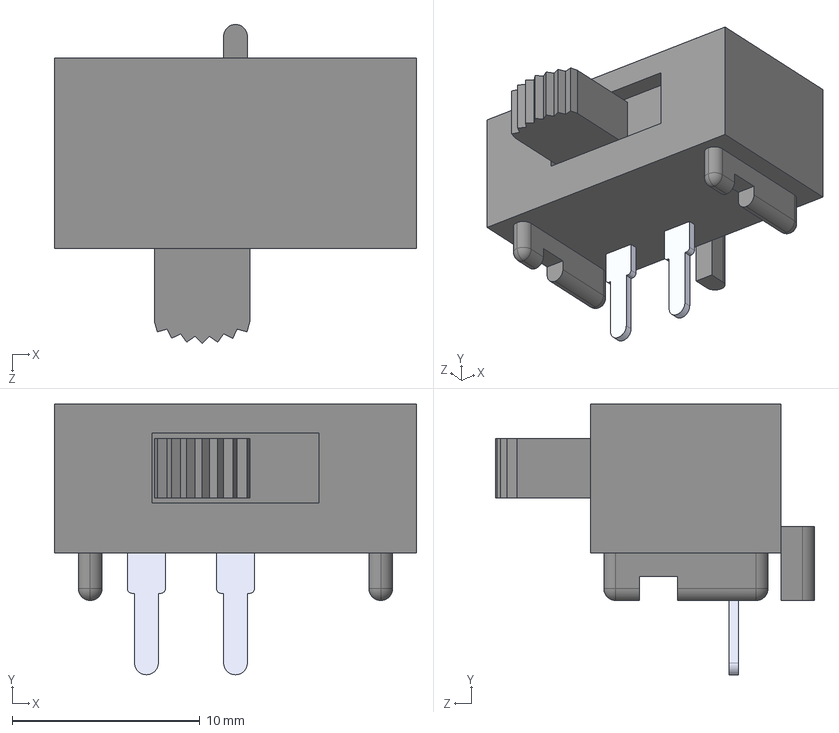
[picture p72: CAD file, 2024-10-07]
table-2/kicad_libraries/My_Libraries/SPSTL101011ML04Q.STEP
19.3 x 14.4 x 17.0 mm
