Jahjahhhh/projet5/table-2/kicad_libraries/My_Libraries/BHX1-1025-SM.STEP

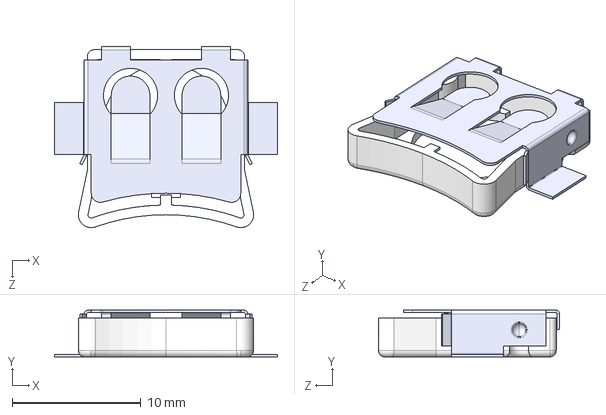
[picture p73: CAD file, 2024-10-07]
table-2/kicad_libraries/My_Libraries/BHX1-1025-SM.STEP
17.3 x 3.63 x 14.1 mm
