Jahjahhhh/projet5/table-2/kicad_libraries/My_Libraries/LQH43CN220K03L.STEP

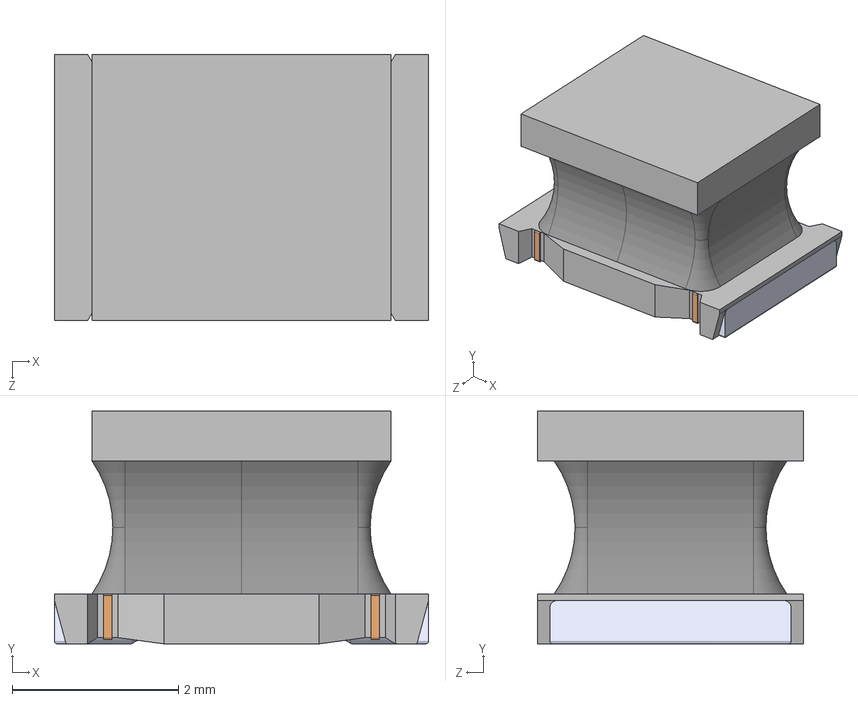
[picture p74: CAD file, 2024-10-07]
table-2/kicad_libraries/My_Libraries/LQH43CN220K03L.STEP
4.50 x 2.80 x 3.20 mm
