Jahjahhhh/projet5/table-2/kicad_libraries/My_Libraries/SDCL1V2512-R.STEP

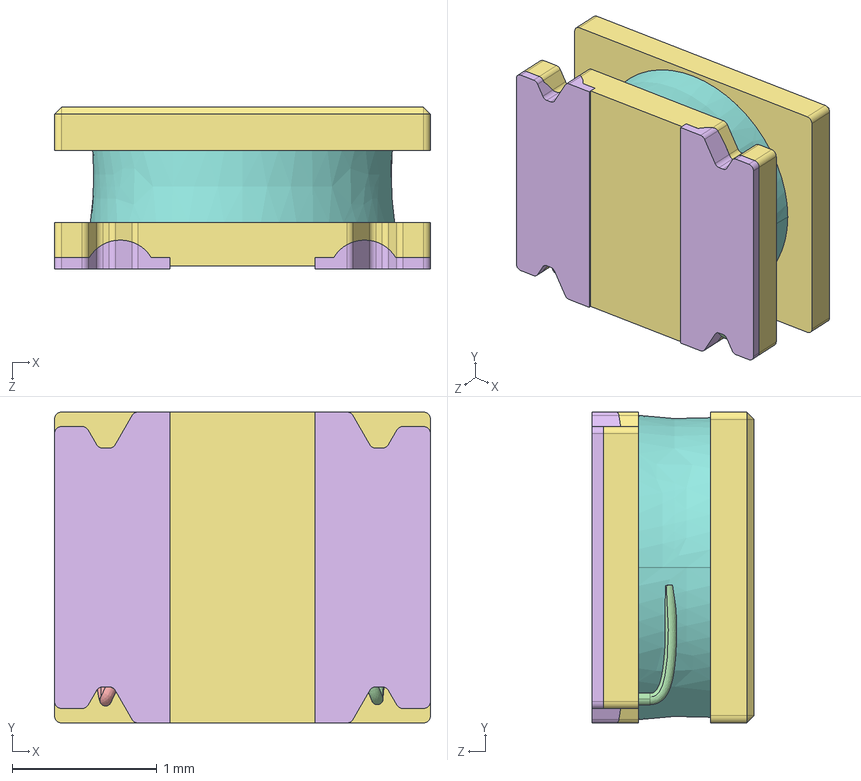
[picture p75: CAD file, 2024-10-07]
table-2/kicad_libraries/My_Libraries/SDCL1V2512-R.STEP
2.60 x 2.15 x 1.12 mm
