Jahjahhhh/projet5/table-2/kicad_libraries/My_Libraries/CPC1998J_IXY.step

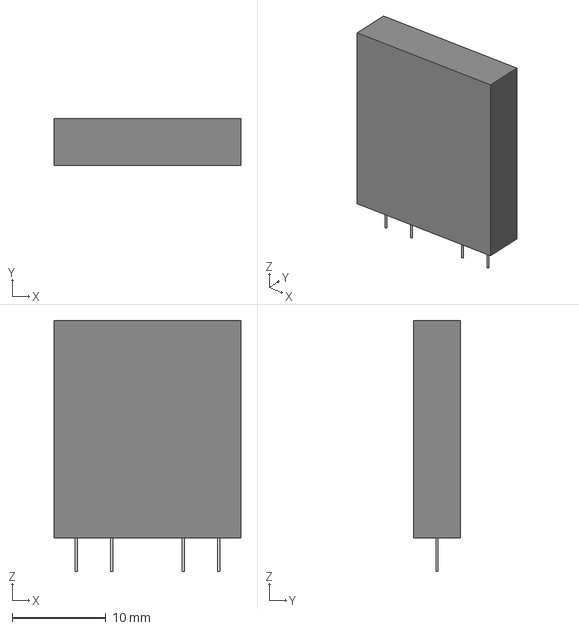
[picture p76: CAD file, 2024-10-07]
table-2/kicad_libraries/My_Libraries/CPC1998J_IXY.step
19.9 x 5.03 x 26.8 mm
