Jahjahhhh/projet5/table-2/kicad_libraries/My_Libraries/Tactile_TL3301.stp

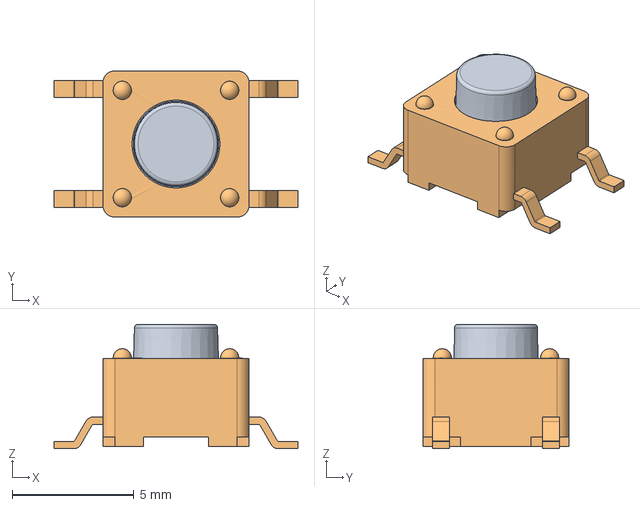
[picture p77: CAD file, 2024-10-07]
table-2/kicad_libraries/My_Libraries/Tactile_TL3301.stp
10.0 x 6.00 x 5.10 mm
