Jahjahhhh/projet5/table-2/kicad_libraries/My_Libraries/HC_05 Blue Tooth.stp

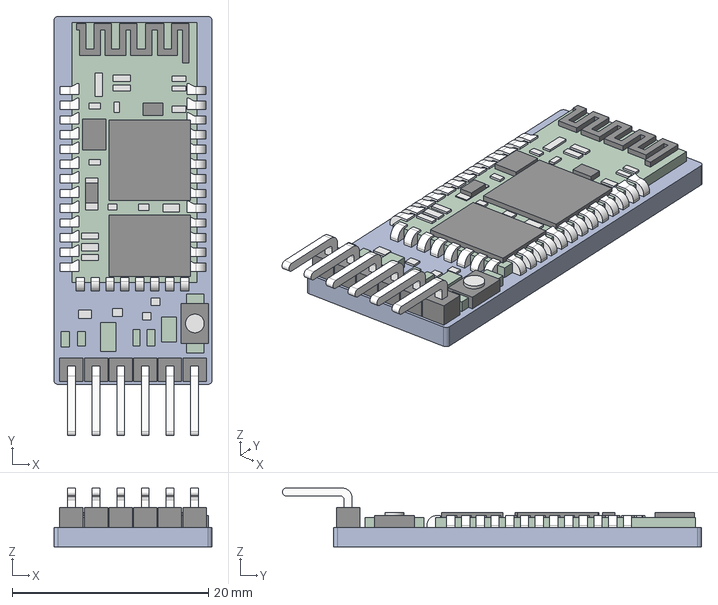
[picture p78: CAD file, 2024-10-07]
table-2/kicad_libraries/My_Libraries/HC_05 Blue Tooth.stp
16.1 x 42.7 x 6.00 mm
