Jahjahhhh/projet5/table-2/kicad_libraries/My_Libraries/B3B-XH-AM.STEP

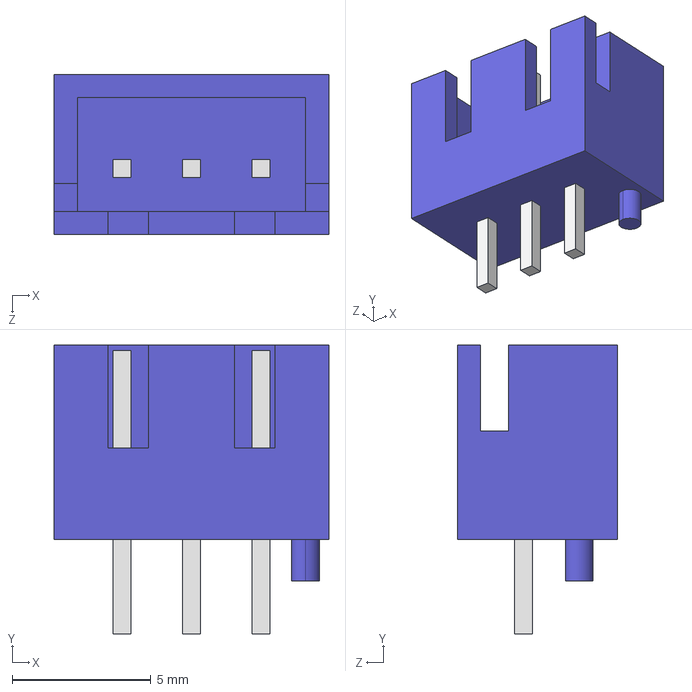
[picture p79: CAD file, 2024-10-07]
table-2/kicad_libraries/My_Libraries/B3B-XH-AM.STEP
9.90 x 10.4 x 5.75 mm
