Jahjahhhh/projet5/table-2/kicad_libraries/My_Libraries/LCD Nokia 5110.step

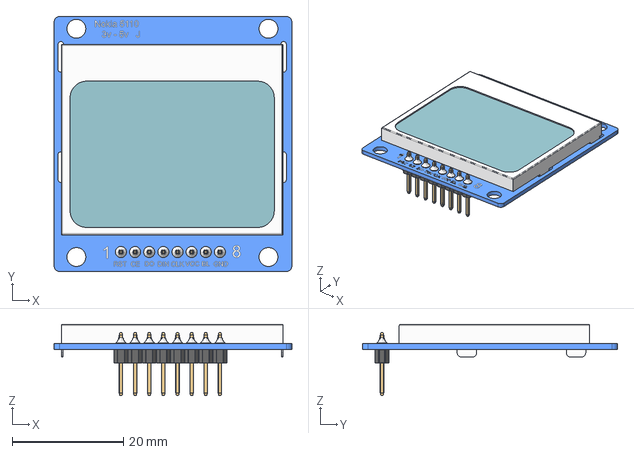
[picture p80: CAD file, 2024-10-07]
table-2/kicad_libraries/My_Libraries/LCD Nokia 5110.step
42.7 x 45.8 x 12.8 mm
Nokia_5110_Display
Male Pin Header x 8
