Jahjahhhh/projet5/table-2/kicad_libraries/My_Libraries/FH34SRJ-24S.STEP

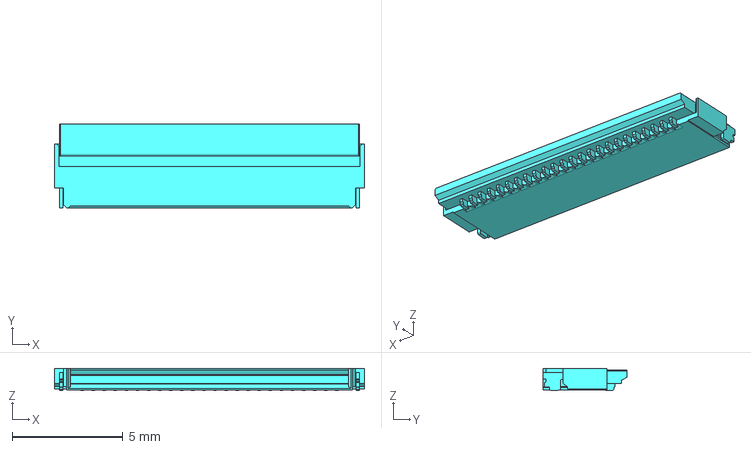
[picture p81: CAD file, 2024-10-07]
table-2/kicad_libraries/My_Libraries/FH34SRJ-24S.STEP
14.0 x 3.80 x 1.00 mm
