Jahjahhhh/projet5/table-2/kicad_libraries/My_Libraries/LoRa_Module_RA-02_AiThinker.step

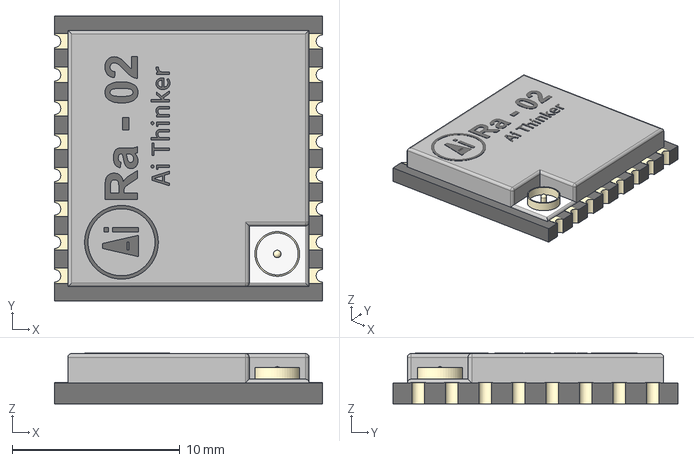
[picture p82: CAD file, 2024-10-07]
table-2/kicad_libraries/My_Libraries/LoRa_Module_RA-02_AiThinker.step
16.0 x 17.0 x 3.03 mm
