Jahjahhhh/projet5/table-2/kicad_libraries/My_Libraries/wemos_d1_mini_Coupe.step

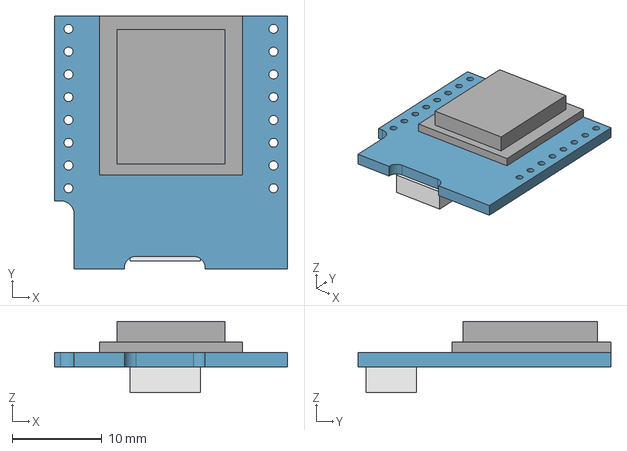
[picture p83: CAD file, 2024-10-07]
table-2/kicad_libraries/My_Libraries/wemos_d1_mini_Coupe.step
26.0 x 28.2 x 7.95 mm
