Jahjahhhh/projet5/table-2/kicad_libraries/My_Libraries/User Library-XBeeProS_AG1.step

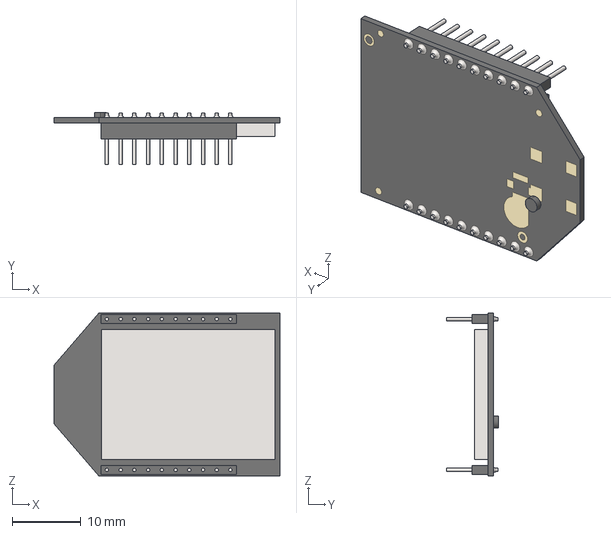
[picture p84: CAD file, 2024-10-07]
table-2/kicad_libraries/My_Libraries/User Library-XBeeProS_AG1.step
32.9 x 7.60 x 23.7 mm
