Jahjahhhh/projet5/table-2/kicad_libraries/My_Libraries/keystone_PN1049PAG.step

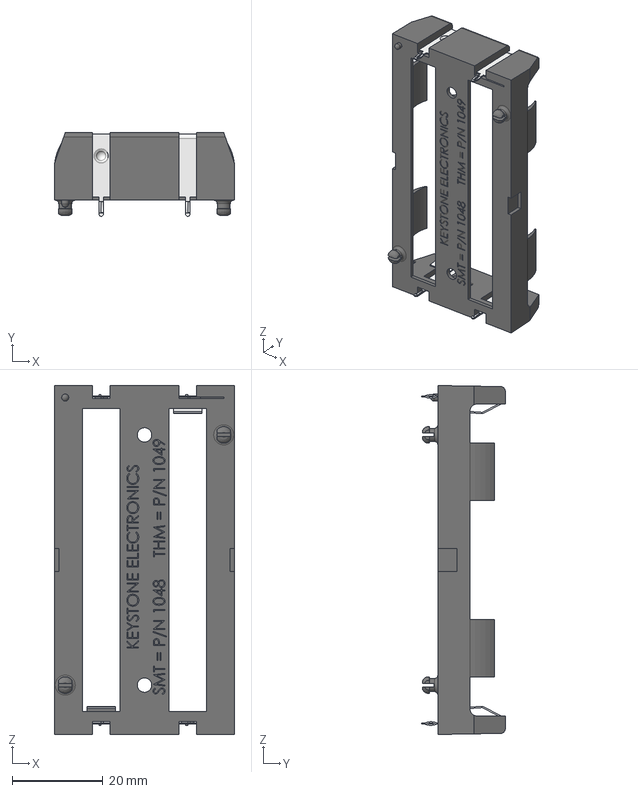
[picture p85: CAD file, 2024-10-07]
table-2/kicad_libraries/My_Libraries/keystone_PN1049PAG.step
39.8 x 18.5 x 77.1 mm
