Jahjahhhh/projet5/table-2/kicad_libraries/My_Libraries/CON_2X20_LATCH.stp

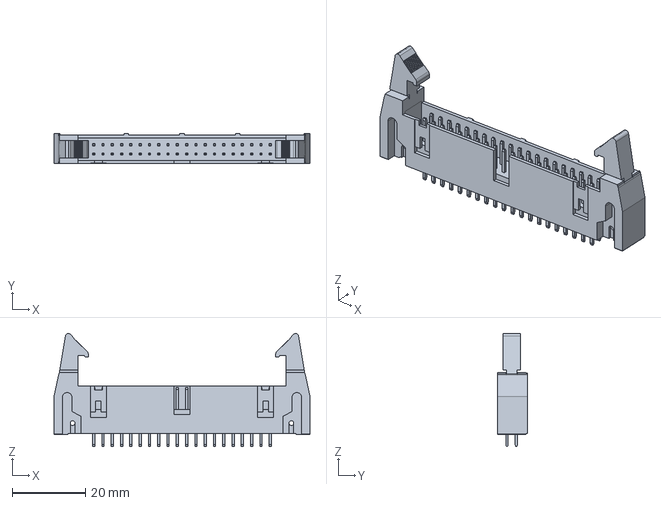
[picture p86: CAD file, 2024-10-07]
table-2/kicad_libraries/My_Libraries/CON_2X20_LATCH.stp
70.0 x 8.30 x 30.9 mm
