Jahjahhhh/projet5/table-2/kicad_libraries/My_Libraries/SCL3300-D01-1_MUR.step

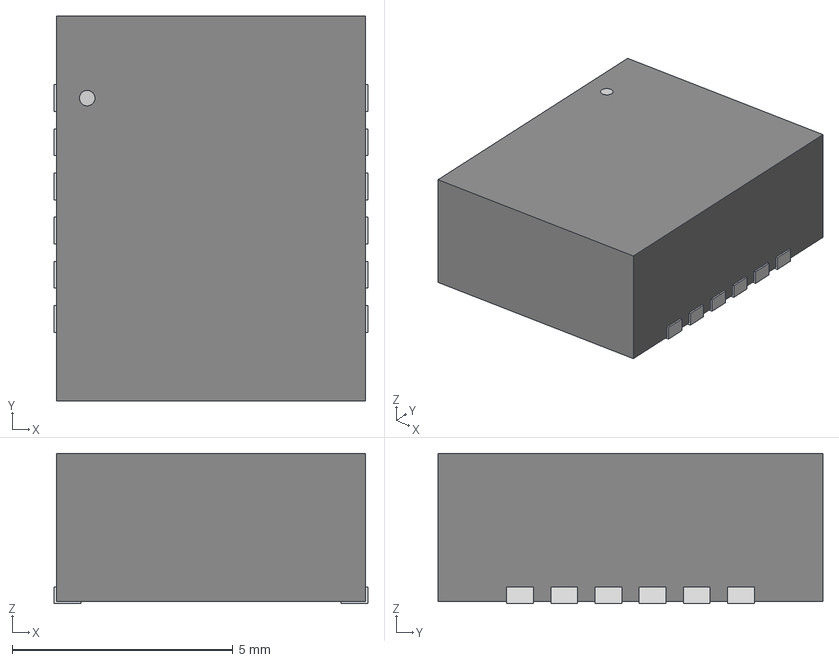
[picture p87: CAD file, 2024-10-07]
table-2/kicad_libraries/My_Libraries/SCL3300-D01-1_MUR.step
7.11 x 8.71 x 3.41 mm
