Jahjahhhh/projet5/table-2/kicad_libraries/My_Libraries/Jack_Stereo.stp

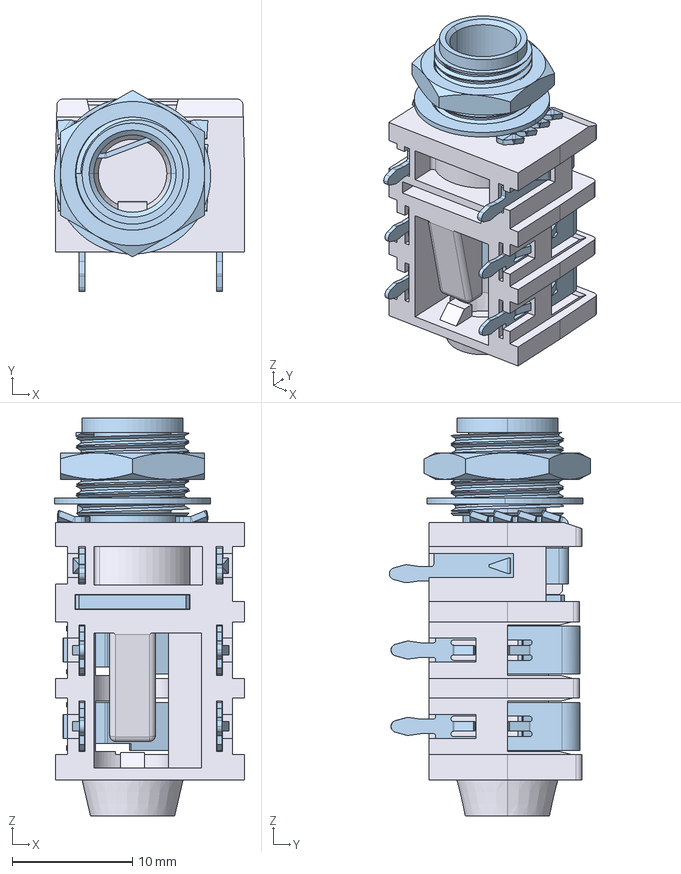
[picture p88: CAD file, 2024-10-07]
table-2/kicad_libraries/My_Libraries/Jack_Stereo.stp
15.8 x 16.7 x 33.1 mm
PJ-629 BIG NUT
PJ-629 FLAT WASHER
SLEEVE
JING x 2
DONG x 2
HOUSE
