Jahjahhhh/projet5/table-2/kicad_libraries/My_Libraries/2908-05WB-MGAG.step

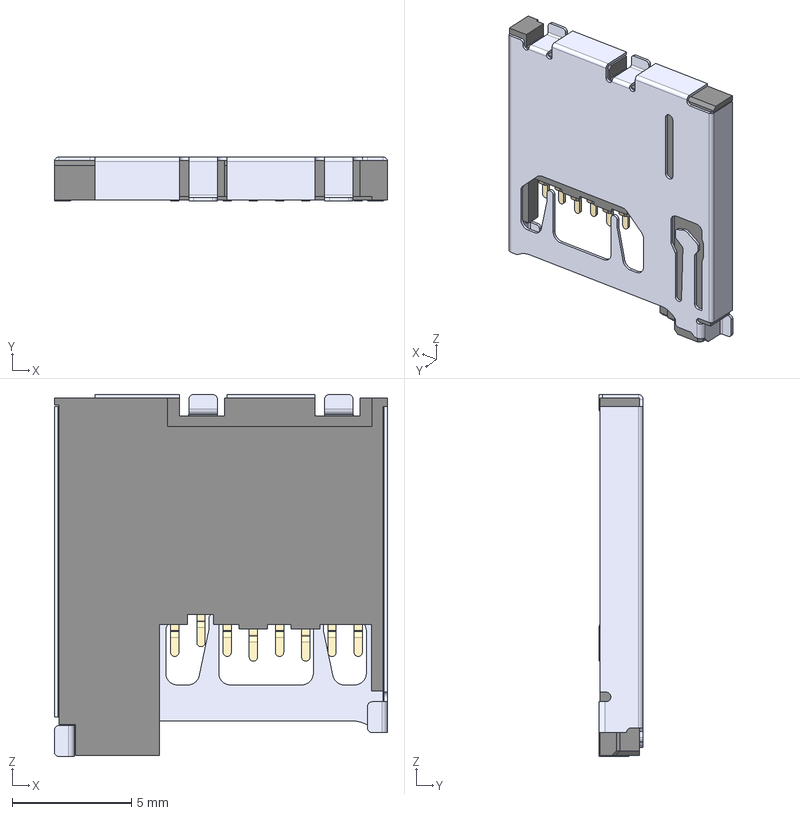
[picture p89: CAD file, 2024-10-07]
table-2/kicad_libraries/My_Libraries/2908-05WB-MGAG.step
14.0 x 1.85 x 15.2 mm
